fTomo-robot/AK4490DAC/.codex-work/power-layout/after.png

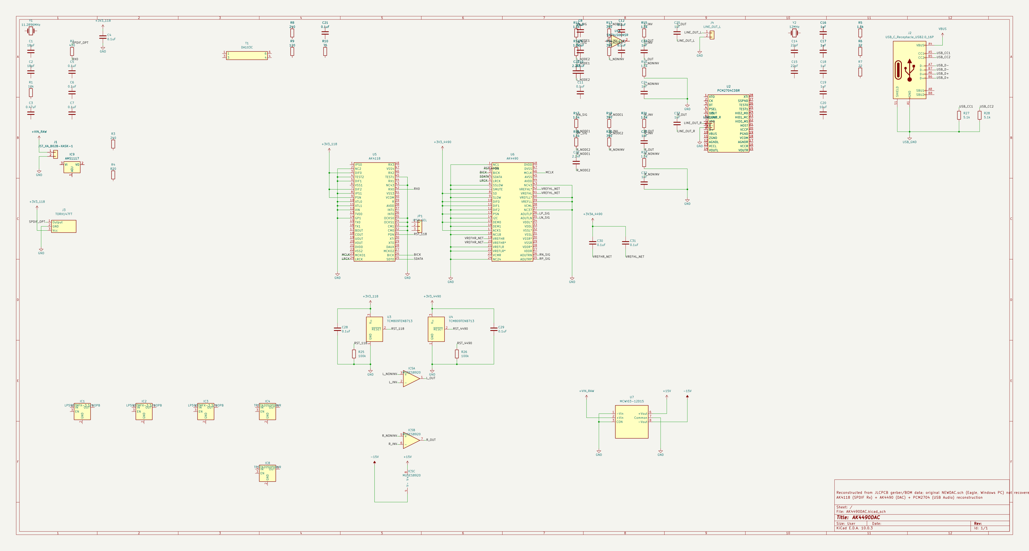
.codex-work/power-layout/after.png
