fTomo-robot/AK4490DAC/.codex-work/power-layout/before.png

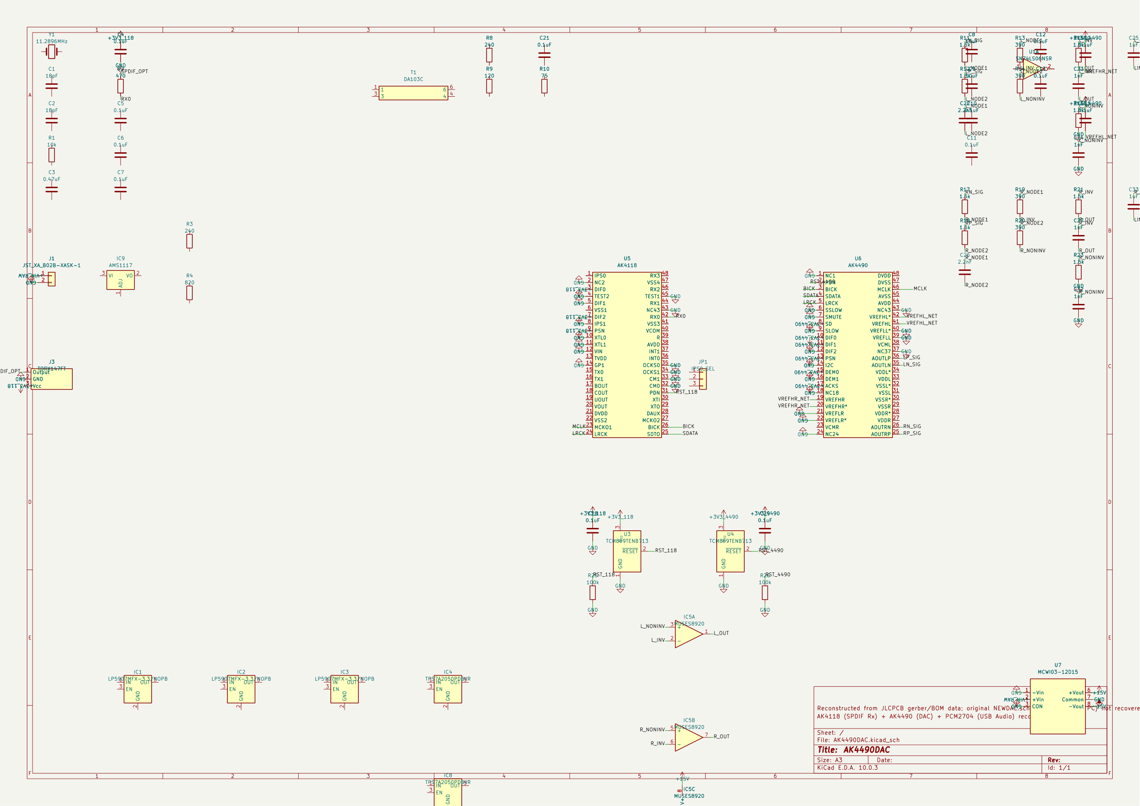
.codex-work/power-layout/before.png
