fTomo-robot/AK4490DAC/.codex-work/power-layout/digital.png

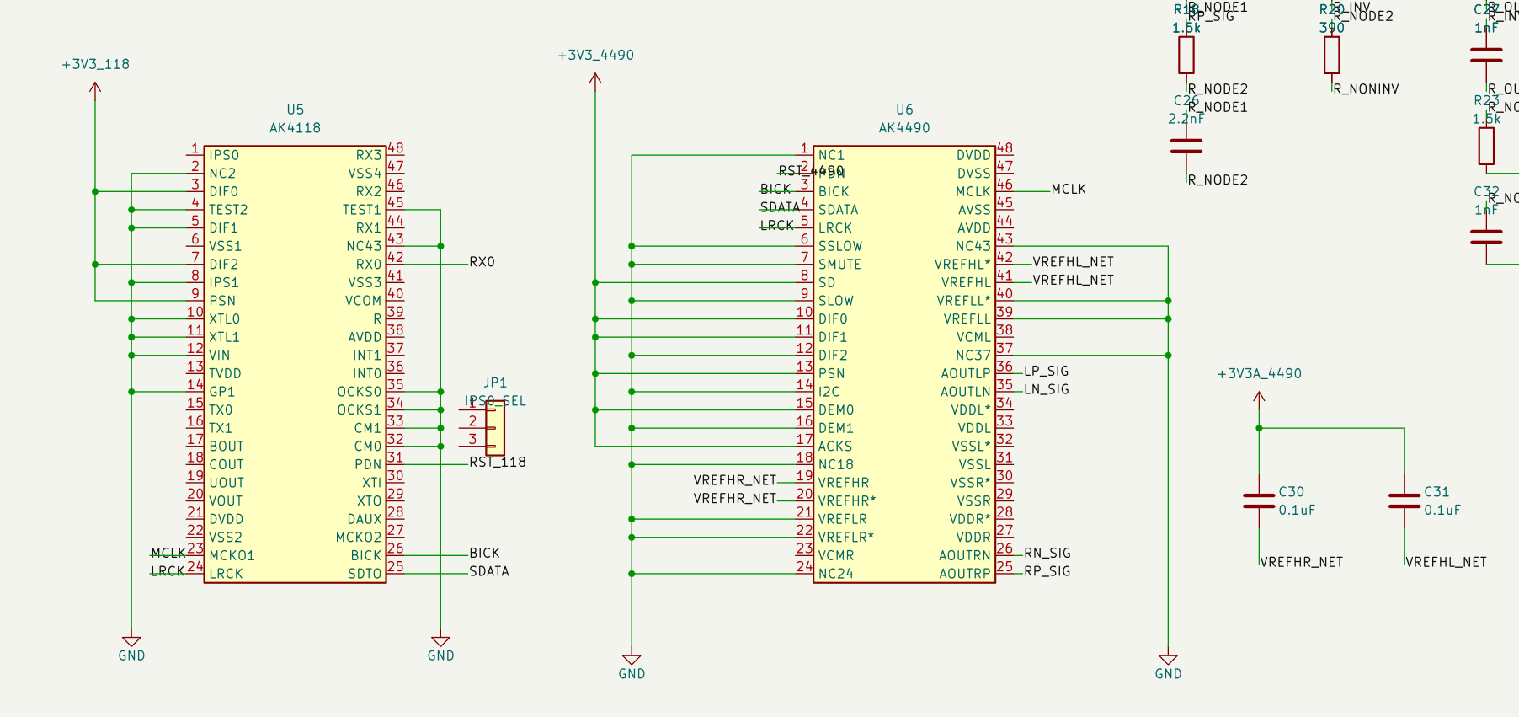
.codex-work/power-layout/digital.png
