fTomo-robot/AK4490DAC/.codex-work/power-layout/input.png

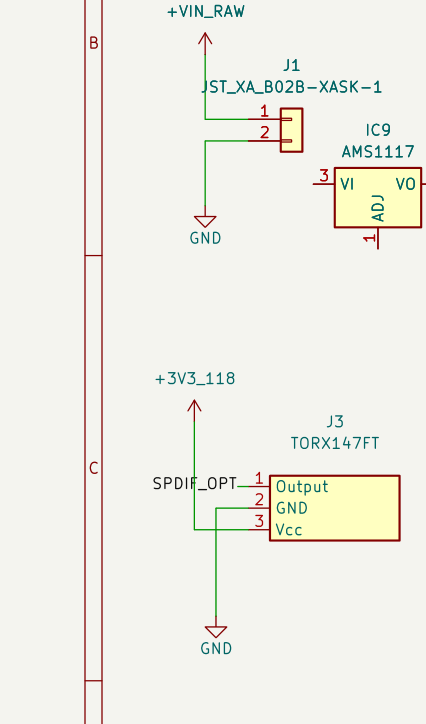
.codex-work/power-layout/input.png
