fTomo-robot/AK4490DAC/.codex-work/power-layout/supply.png

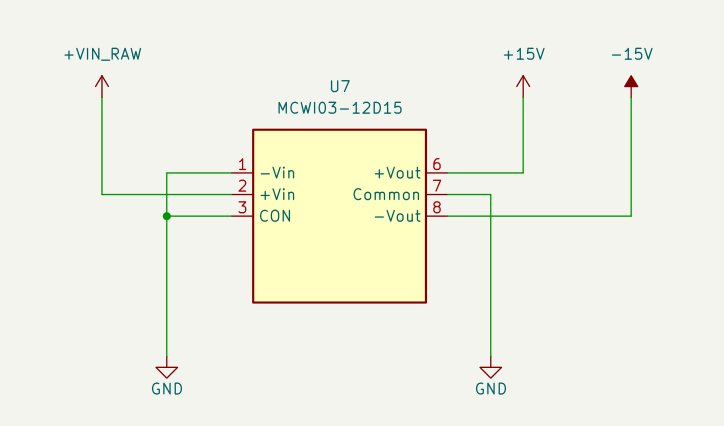
.codex-work/power-layout/supply.png
