fTomo-robot/AK4490DAC/.codex-work/power-layout/usb.png

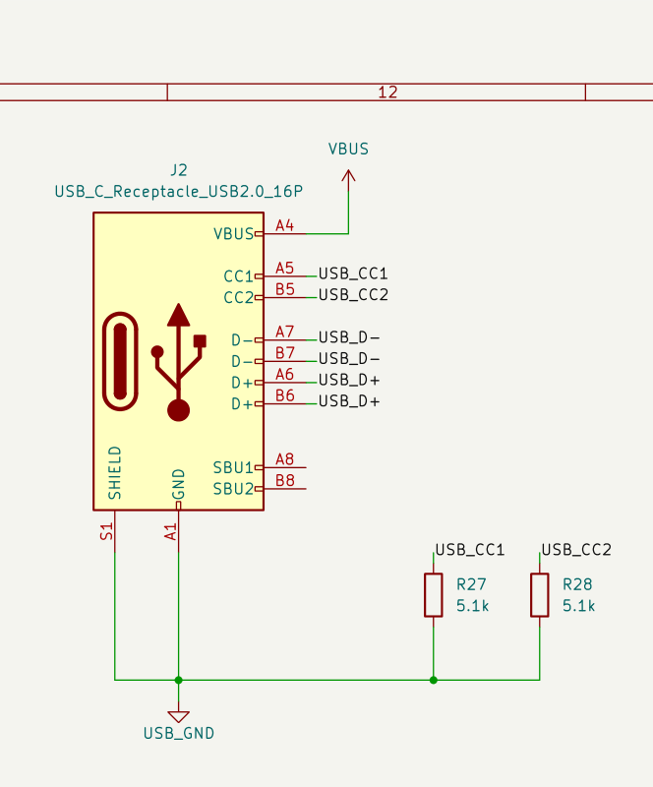
.codex-work/power-layout/usb.png
