fTomo-robot/AK4490DAC/.codex-work/xu316/sources/ak-lpf.png

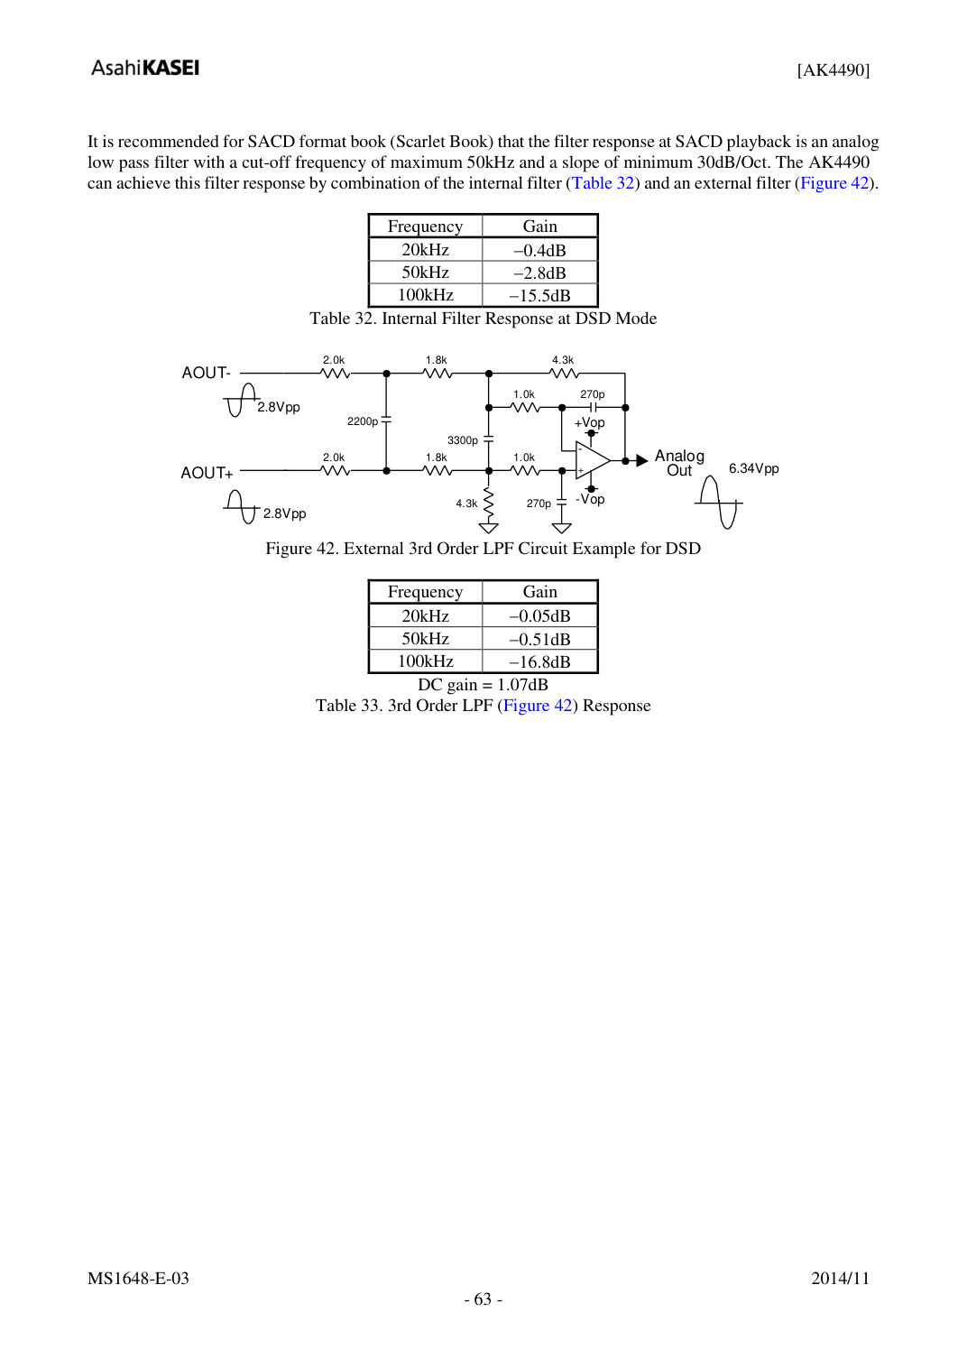
.codex-work/xu316/sources/ak-lpf.png
