fTomo-robot/AK4490DAC/.codex-work/xu316/sources/ak-page60.png

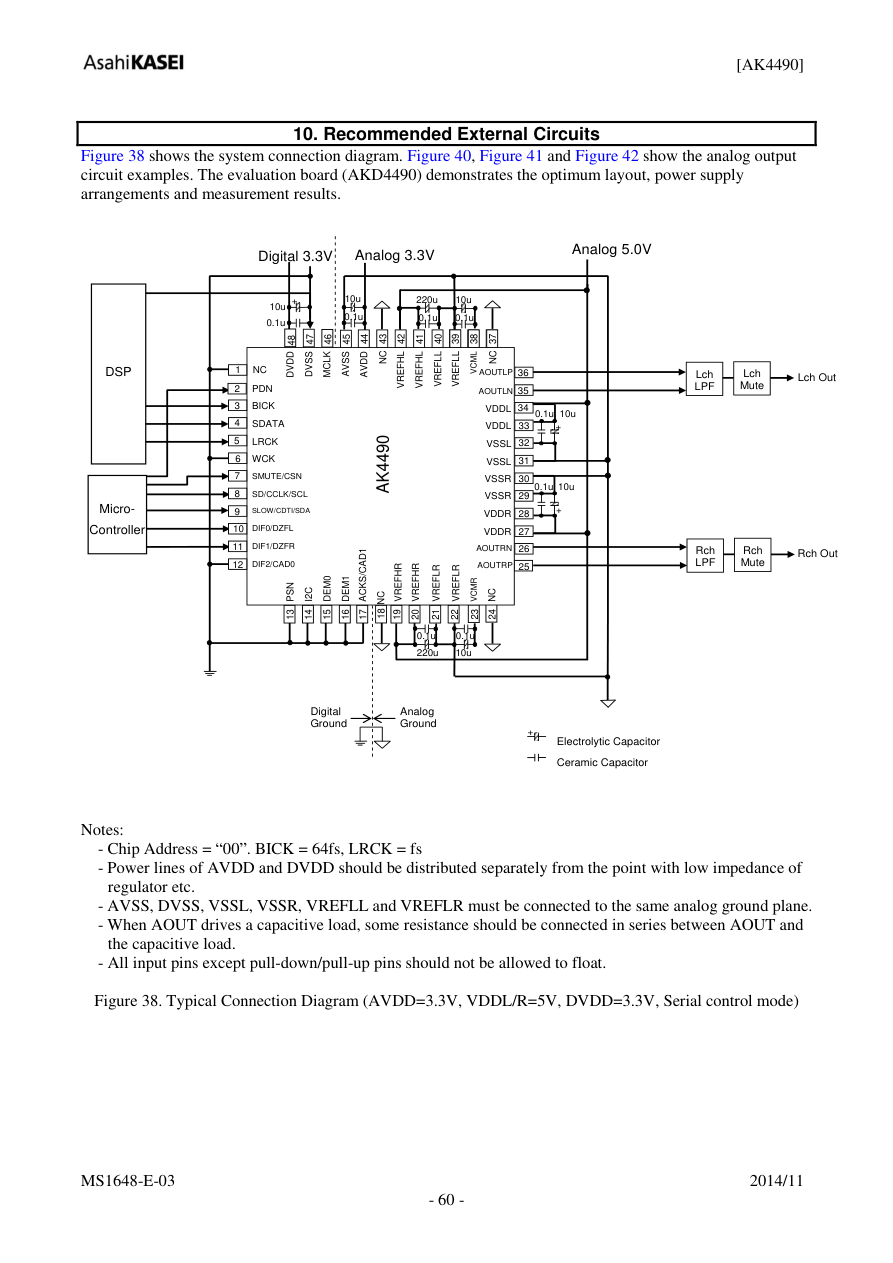
.codex-work/xu316/sources/ak-page60.png
