fTomo-robot/AK4490DAC/.codex-work/xu316/sources/xmos-page49.png

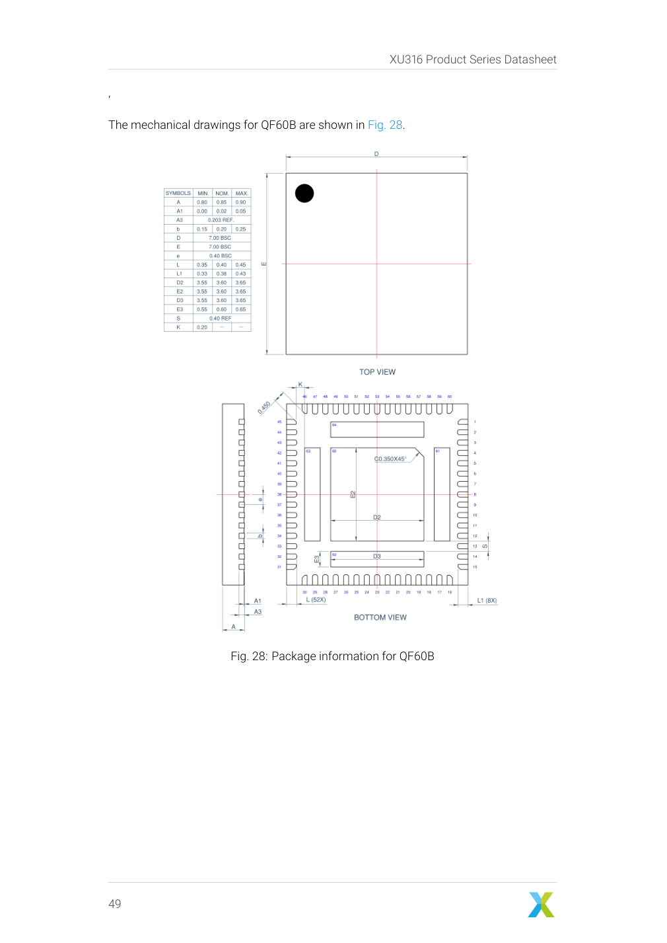
.codex-work/xu316/sources/xmos-page49.png
