fTomo-robot/AK4490DAC/.codex-work/xu316/sources/xmos-page51.png

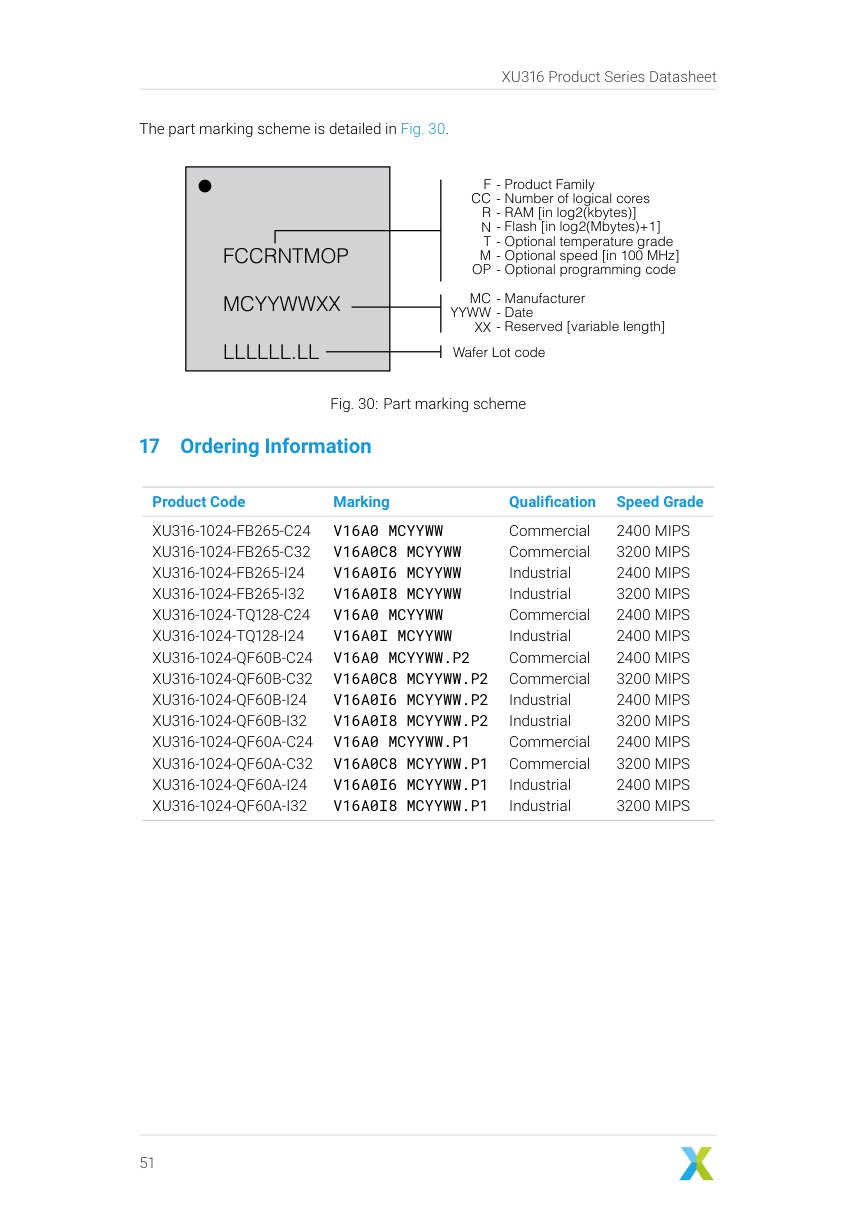
.codex-work/xu316/sources/xmos-page51.png
