fTomo-robot/AK4490DAC/.codex-work/xu316/sources/xmos-page111.png

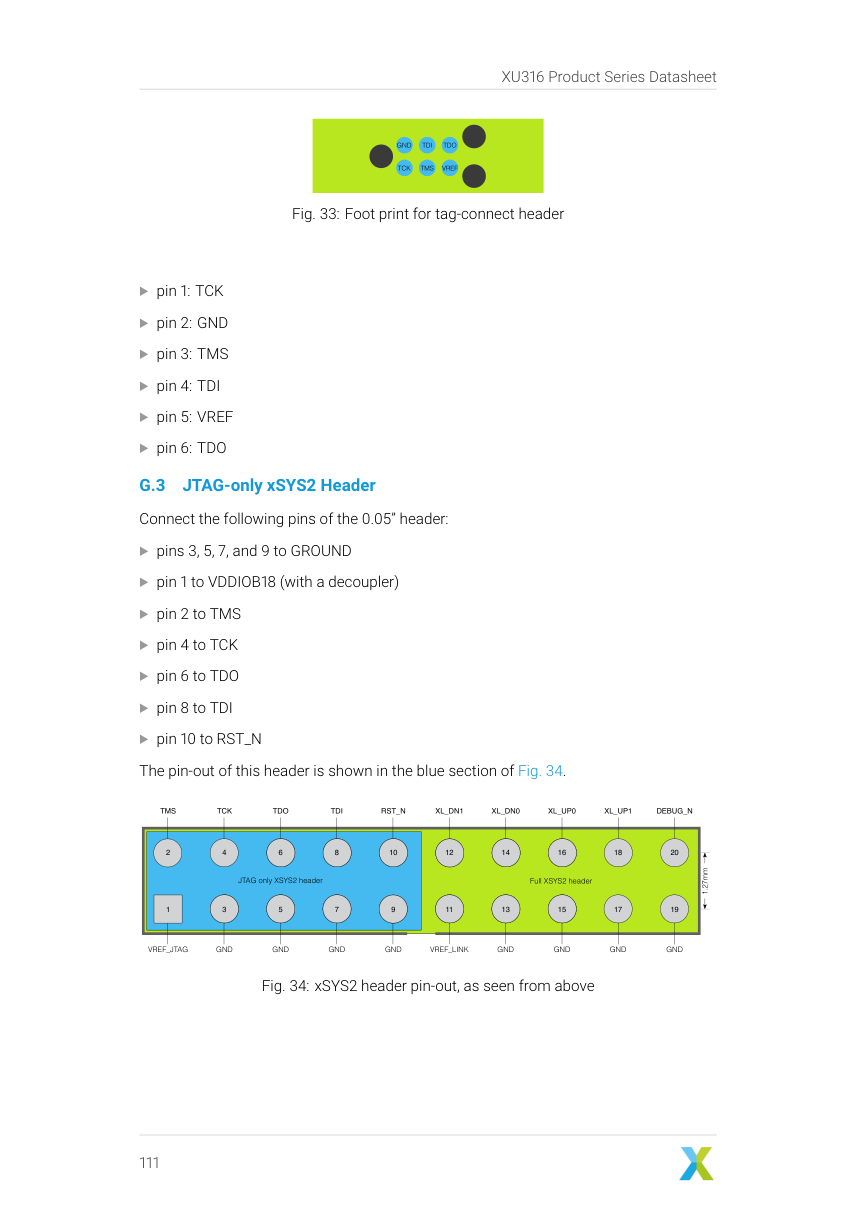
.codex-work/xu316/sources/xmos-page111.png
