fTomo-robot/AK4490DAC/.wiring-cleanup/after.png

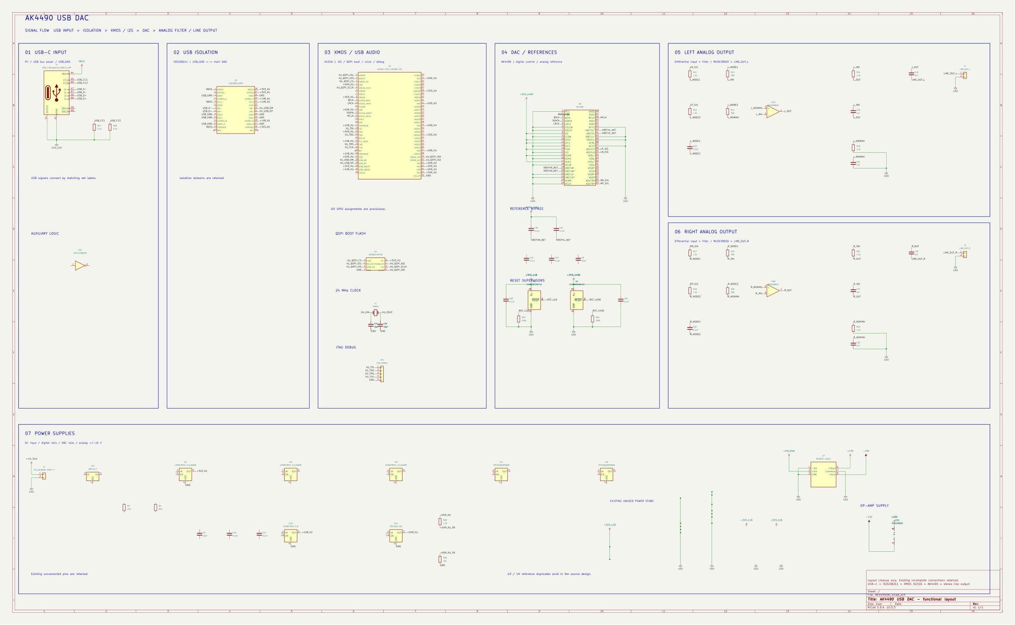
.wiring-cleanup/after.png
