fTomo-robot/AK4490DAC/.wiring-cleanup/before.png

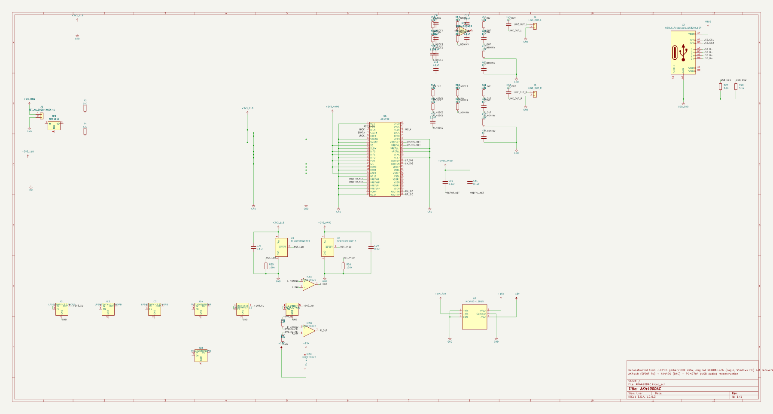
.wiring-cleanup/before.png
