fTomo-robot/AK4490DAC/.wiring-cleanup/final.png

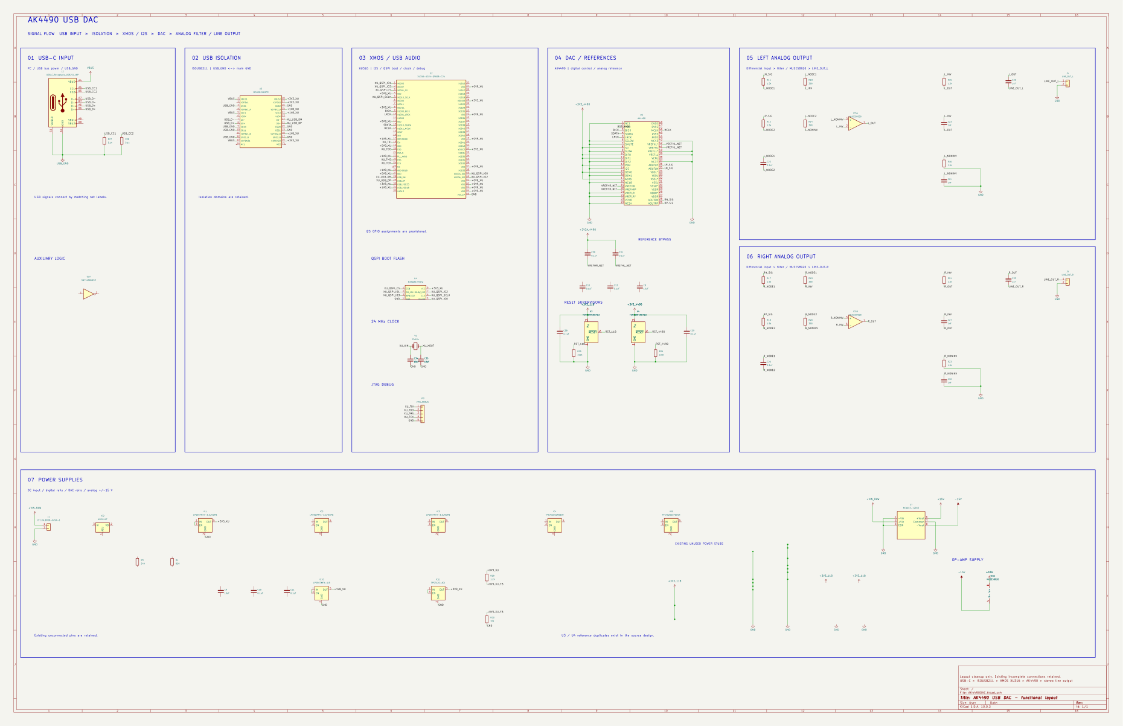
.wiring-cleanup/final.png
