fTomo-robot/AK4490DAC/AK4490DAC.kicad_sch

## KiCad design AK4490DAC.kicad_sch (2026-09-14, an earlier design)

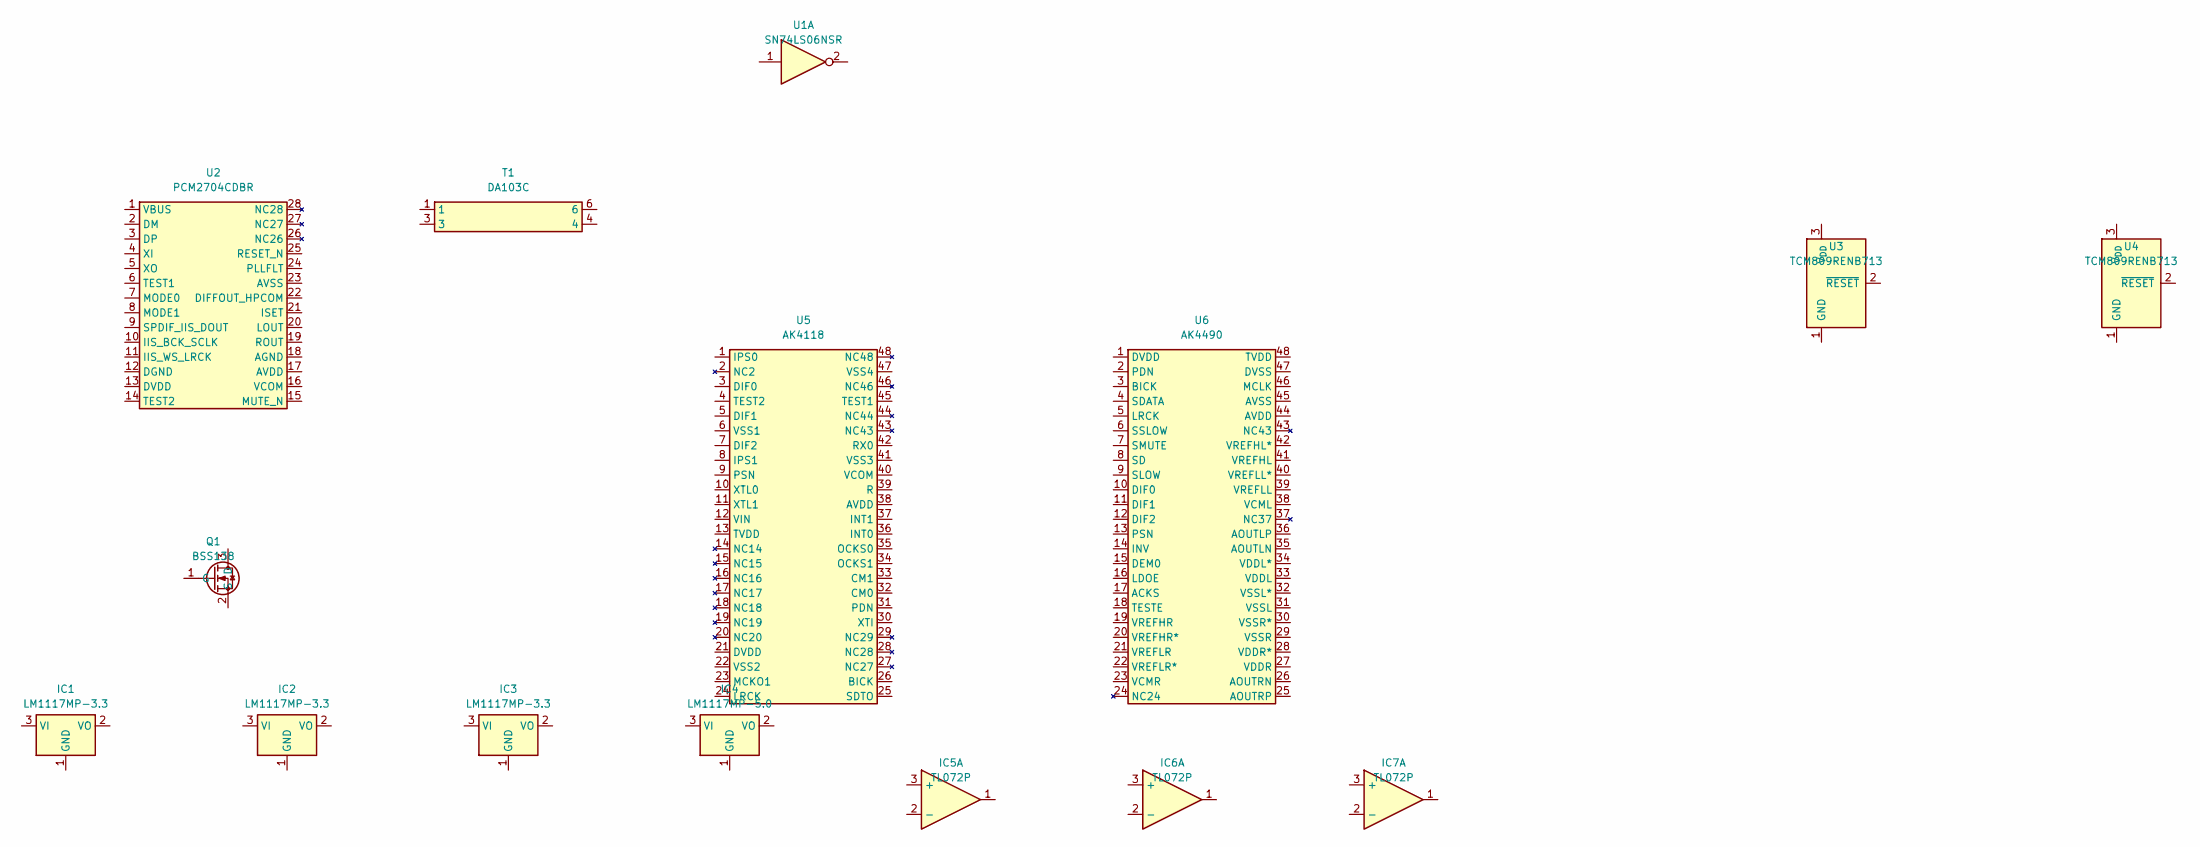
[picture p27: schematic AK4490DAC.kicad_sch]

Parts:
IC1, IC2, IC3: LM1117MP-3.3; SOT-223-3_TabPin2
IC4: LM1117MP-5.0; SOT-223-3_TabPin2
IC5, IC6, IC7: TL072P; DIP-8_W7.62mm
Q1: BSS138; SOT-23
T1: DA103C; DA103C_MUR
U1: SN74LS06NSR; SOIC-14_3.9x8.7mm_P1.27mm
U2: PCM2704CDBR; SSOP-28_5.3x10.2mm_P0.65mm
U3, U4: TCM809RENB713; SOT-23
U5: AK4118; LQFP-48_7x7mm_P0.5mm
U6: AK4490; LQFP-48_7x7mm_P0.5mm
