fTomo-robot/AK4490DAC/.wiring-cleanup/before.kicad_sch

## KiCad design .wiring-cleanup/before.kicad_sch (2026-09-13)

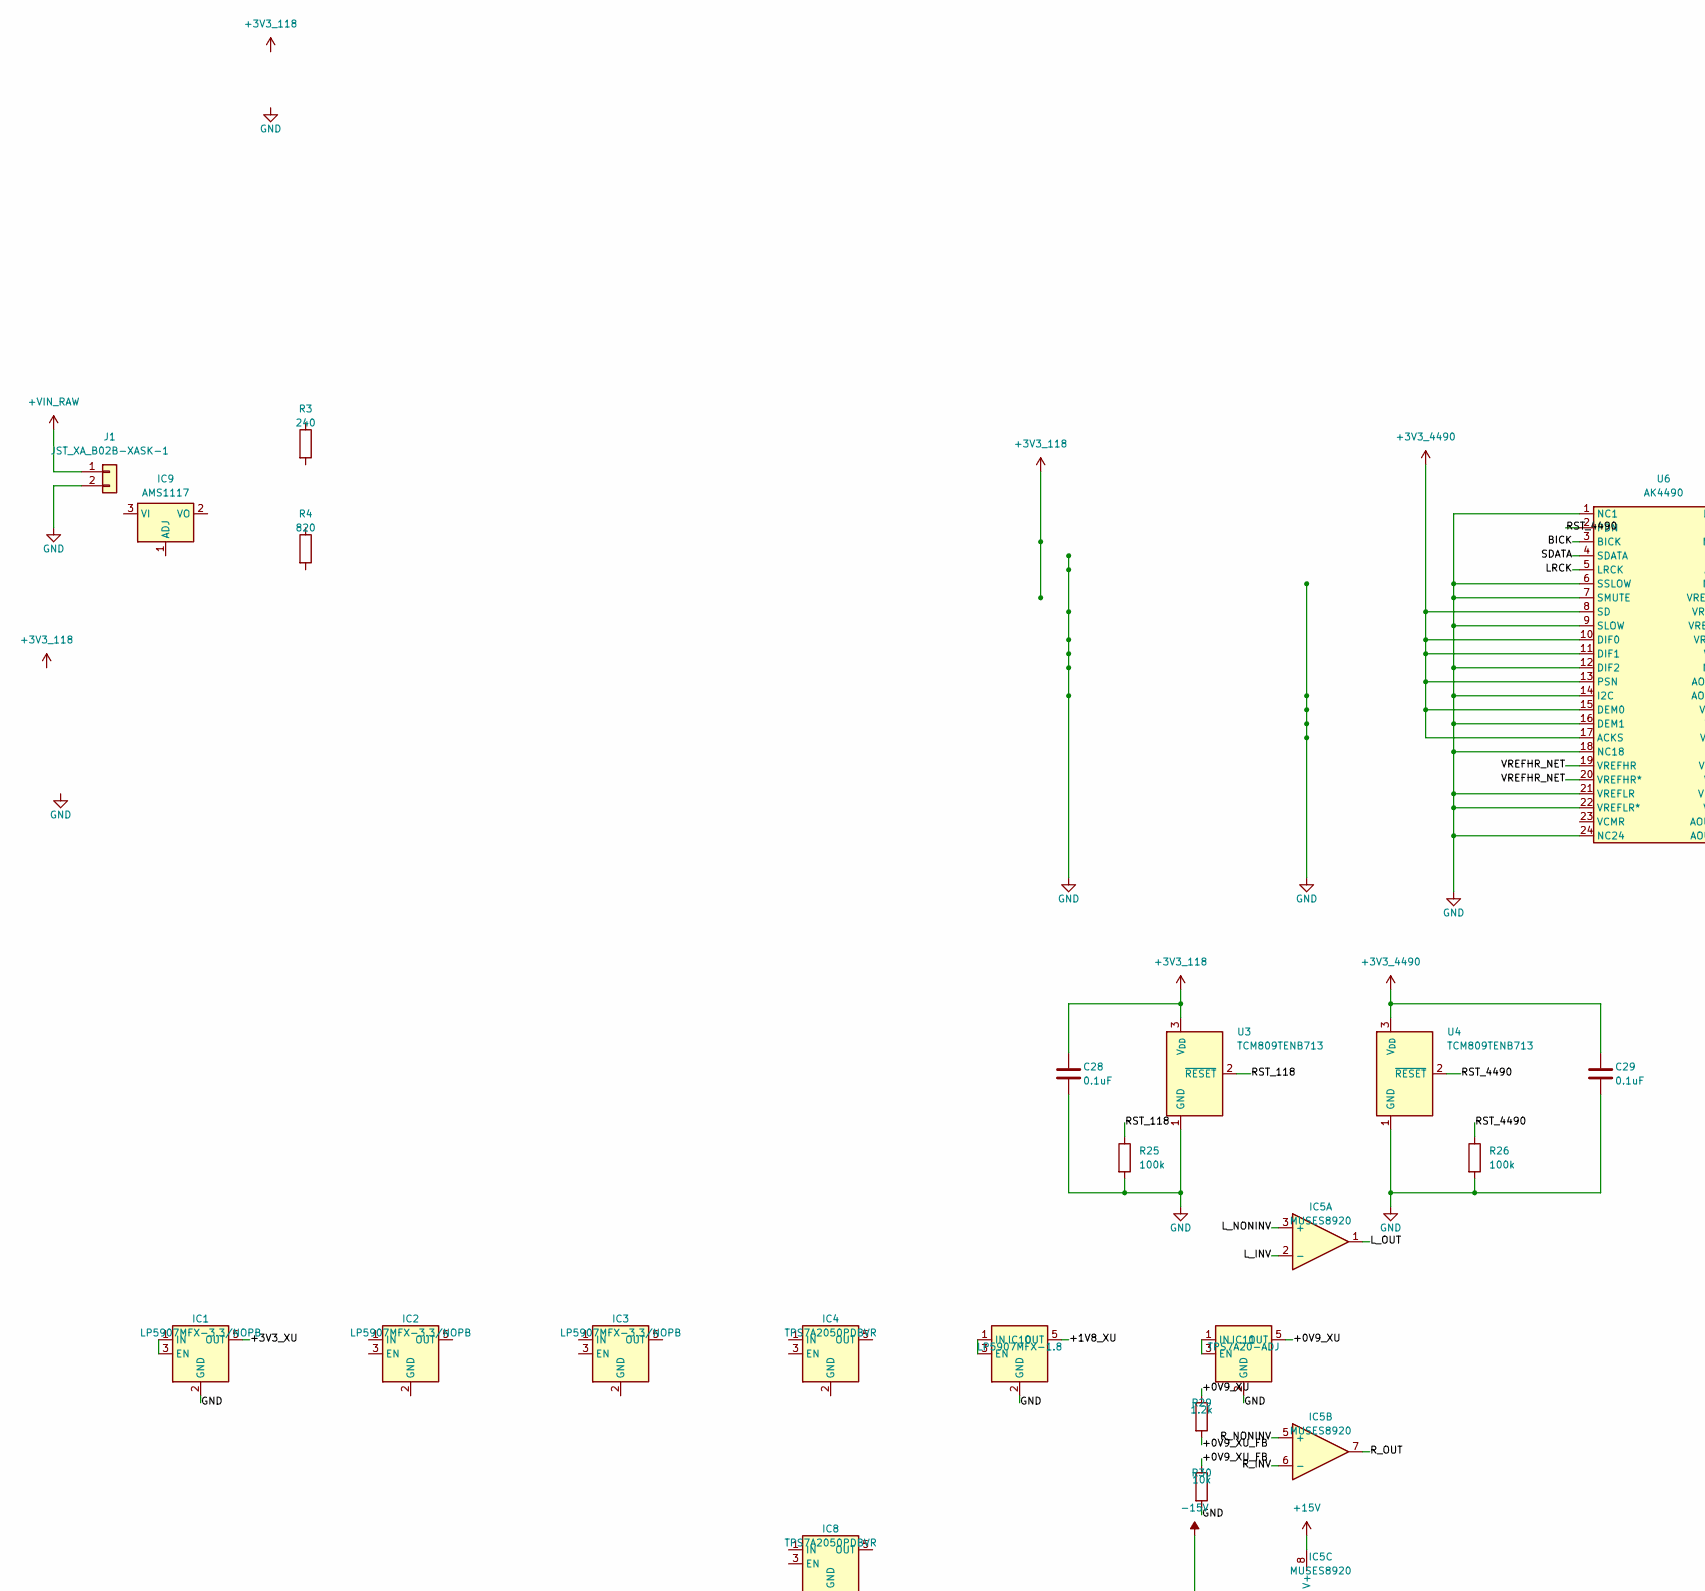
[picture p28: schematic before.kicad_sch, part in row 1, column 1]

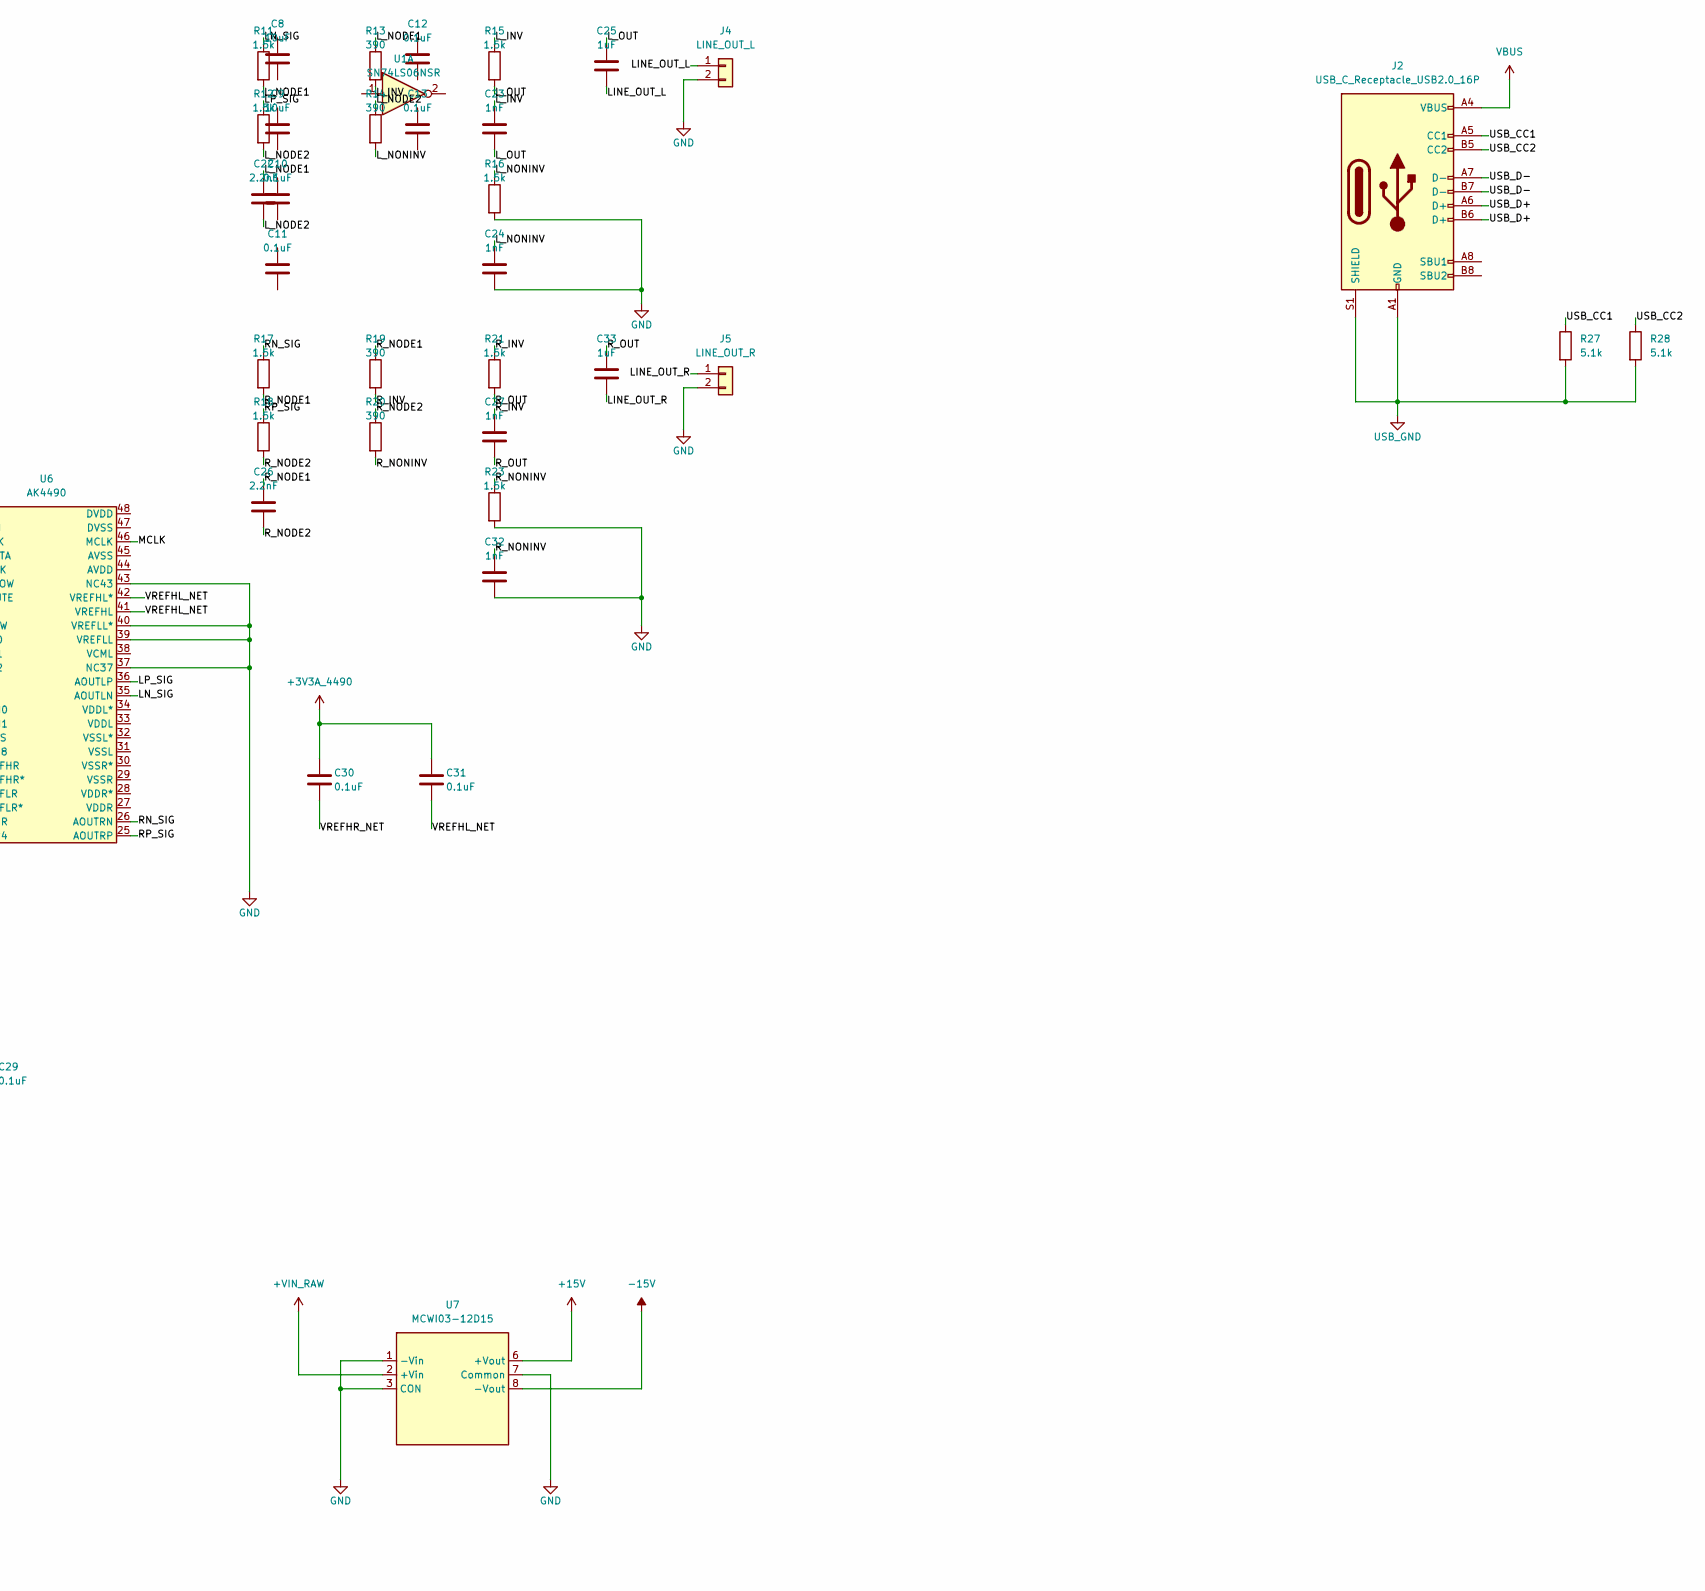
[picture p29: schematic before.kicad_sch, part in row 1, column 2]

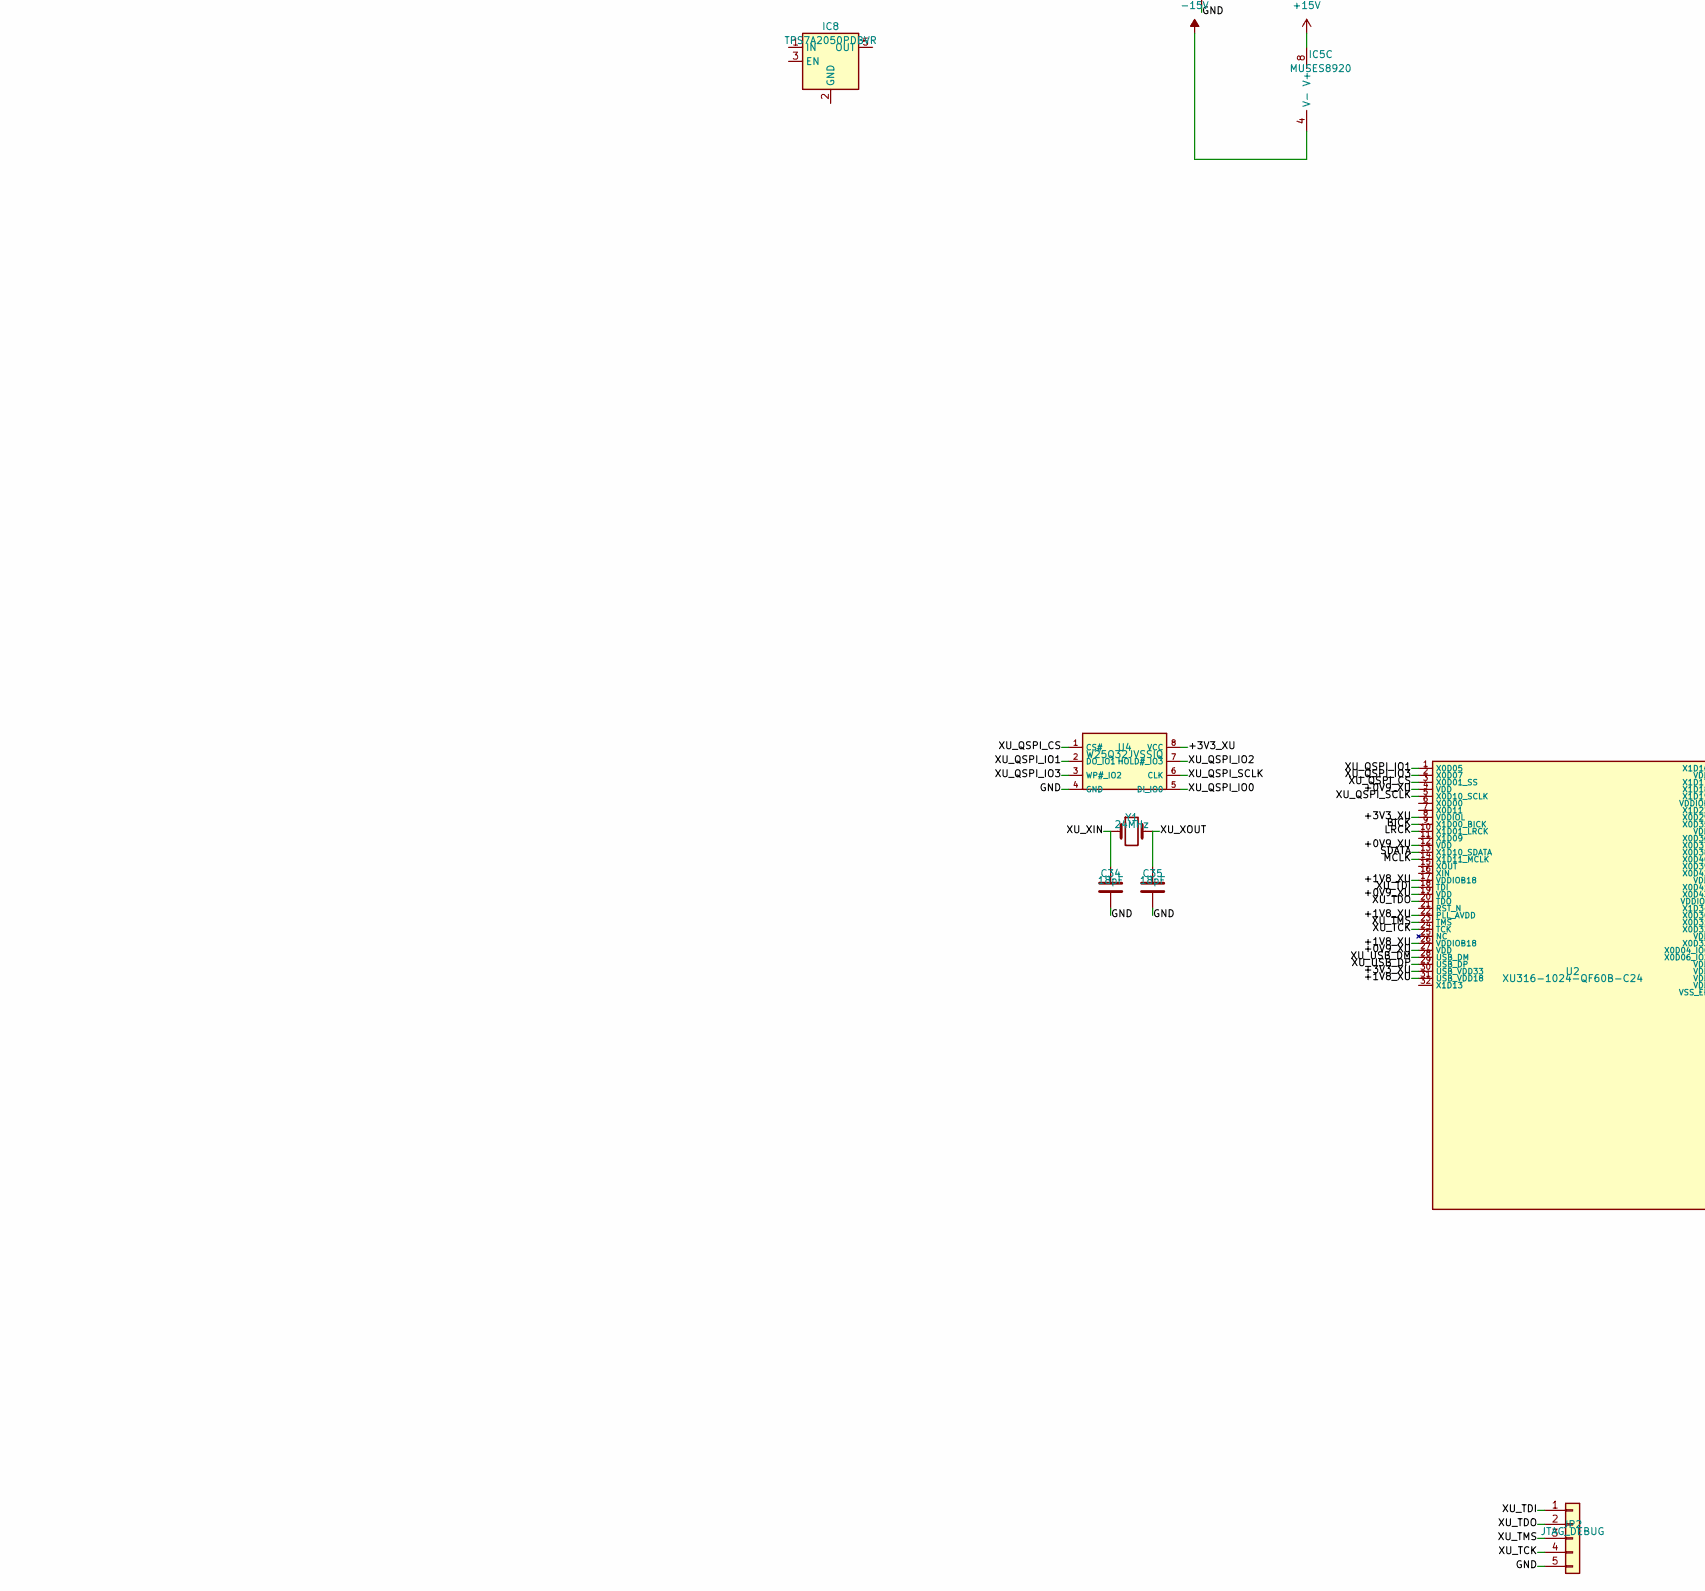
[picture p30: schematic before.kicad_sch, part in row 2, column 1]

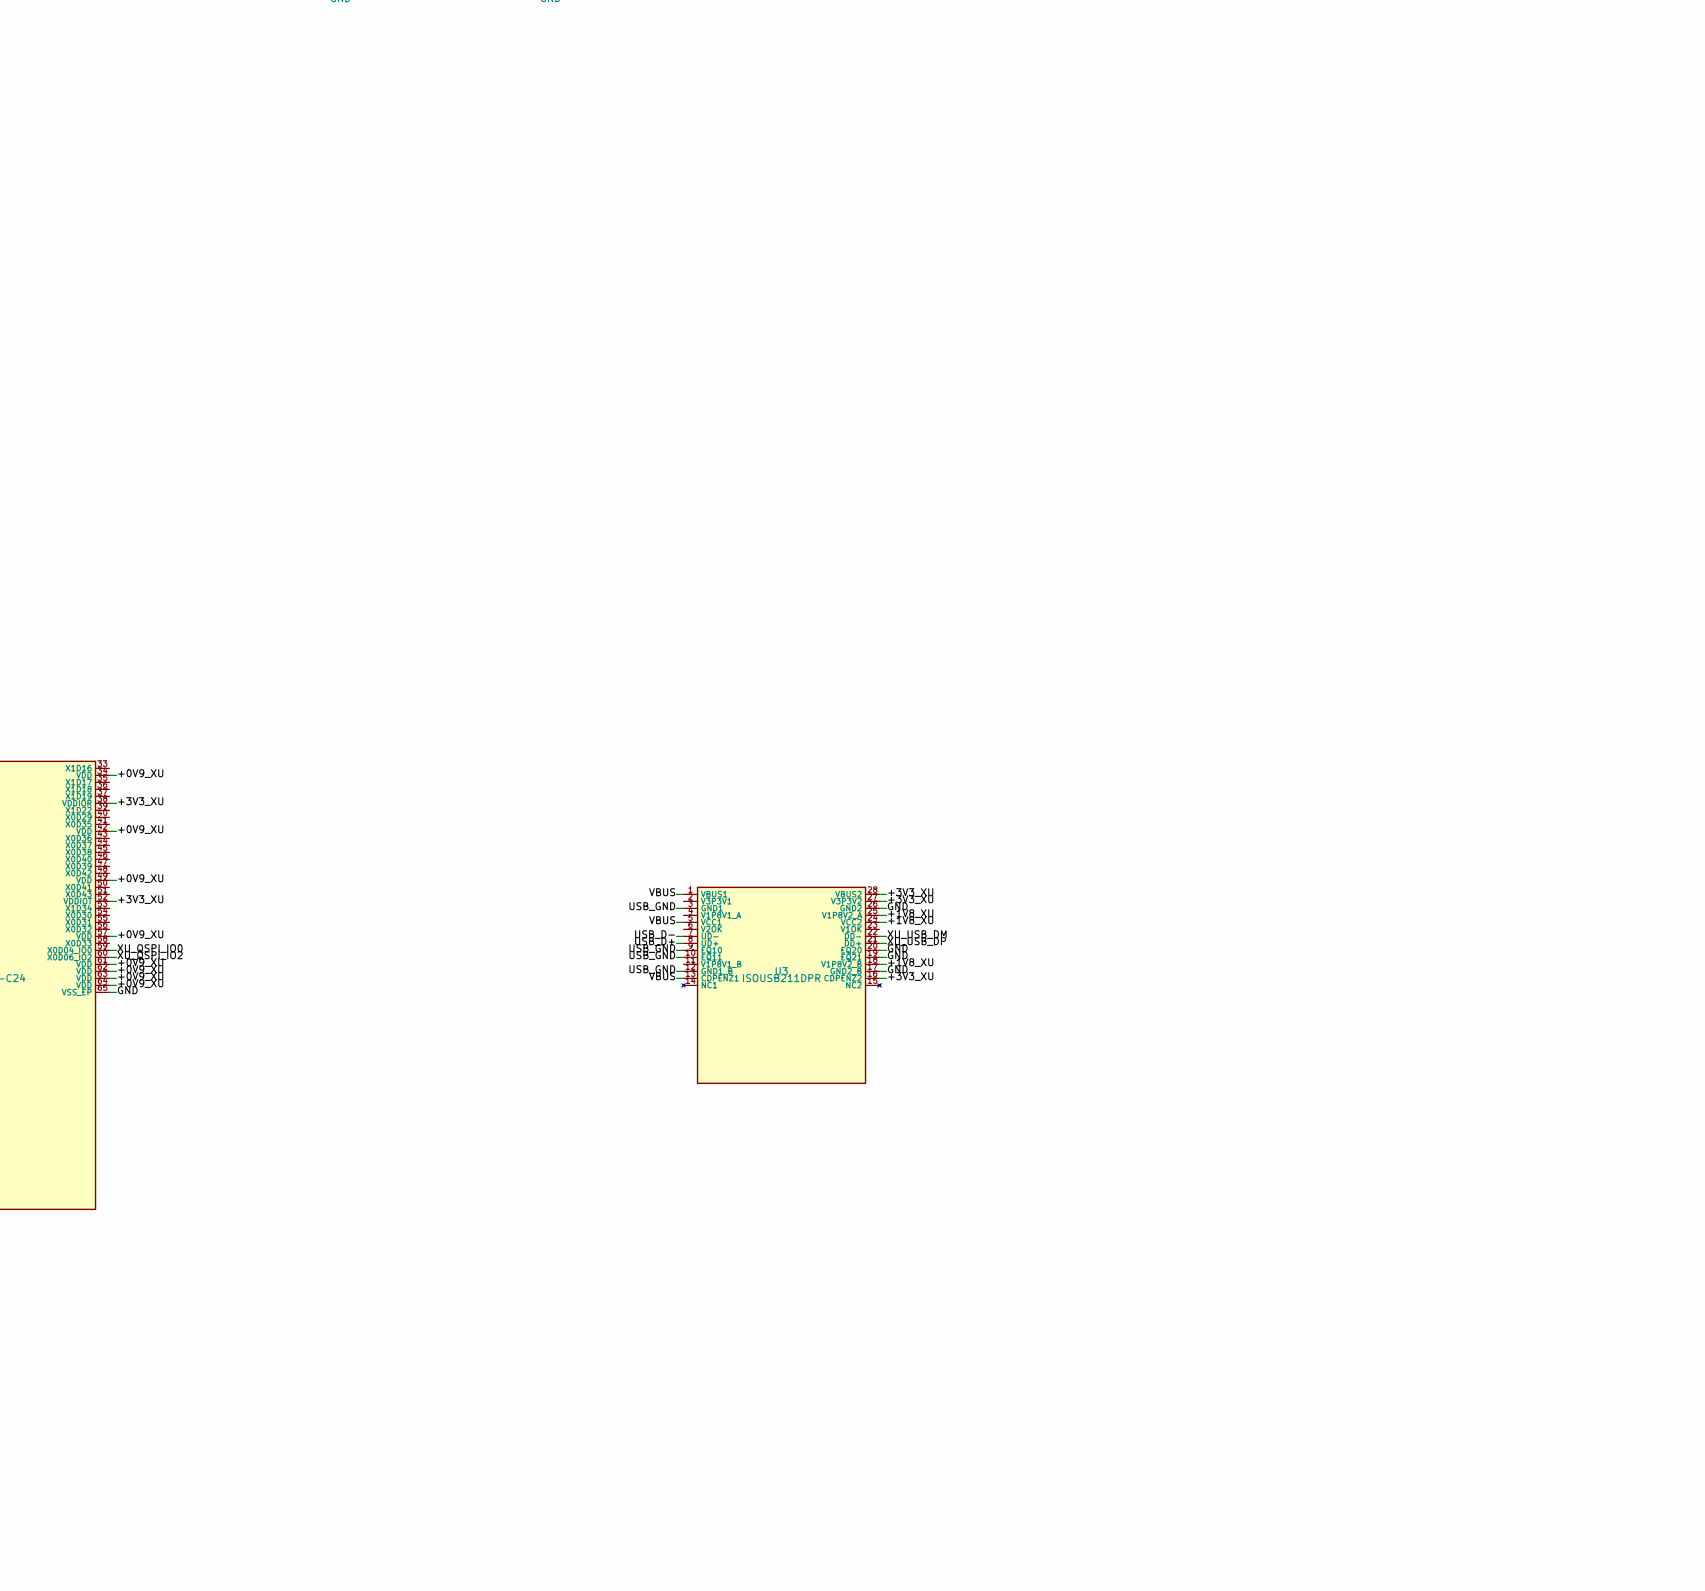
[picture p31: schematic before.kicad_sch, part in row 2, column 2]

Parts:
C8, C9: 10uF; C_0805_2012Metric
C10, C11, C12, C13, C28, C29, C30, C31: 0.1uF; C_0603_1608Metric
C22, C26: 2.2nF; C_0603_1608Metric
C23, C24, C27, C32: 1nF; C_0603_1608Metric
C25, C33: 1uF; C_0603_1608Metric
C34, C35: 18pF; C_0603_1608Metric
IC1, IC2, IC3: LP5907MFX-3.3/NOPB; SOT-23-5
IC4, IC8: TPS7A2050PDBVR; SOT-23-5
IC5: MUSES8920; DIP-8_W7.62mm
IC9: AMS1117; SOT-223-3_TabPin2
IC10: LP5907MFX-1.8; SOT-23-5
IC11: TPS7A20-ADJ; SOT-23-5
J1: JST_XA_B02B-XASK-1; JST_XA_B02B-XASK-1_1x02_P2.50mm_Vertical
J2: USB_C_Receptacle_USB2.0_16P; USB_C_Receptacle_GCT_USB4085
J4: LINE_OUT_L
J5: LINE_OUT_R
JP2: JTAG_DEBUG; PinHeader_1x05_P2.54mm_Vertical
R3: 240; R_0603_1608Metric
R4: 820; R_0603_1608Metric
R11, R12, R15, R16, R17, R18, R21, R23: 1.5k; R_0603_1608Metric
R13, R14, R19, R20: 390; R_0603_1608Metric
R25, R26: 100k; R_0603_1608Metric
R27, R28: 5.1k; R_0603_1608Metric
R29: 1.2k; R_0603_1608Metric
R30: 10k; R_0603_1608Metric
U1: SN74LS06NSR; SOIC-14_3.9x8.7mm_P1.27mm
U2: XU316-1024-QF60B-C24; XU316_QF60B_7x7
U3, U4: TCM809TENB713; SOT-23
U6: AK4490; LQFP-48_7x7mm_P0.5mm
U7: MCWI03-12D15
Y1: 24MHz; Crystal_SMD_3225-4Pin_3.2x2.5mm

Connections:
+0V9_XU: IC11.5 (OUT), R29.1, U2.4 (VDD), U2.12 (VDD), U2.19 (VDD), U2.27 (VDD), U2.34 (VDD), U2.42 (VDD), U2.49 (VDD), U2.57 (VDD), U2.61 (VDD), U2.62 (VDD), U2.63 (VDD), U2.64 (VDD)
+0V9_XU_FB: R29.2, R30.1
+1V8_XU: IC10.5 (OUT), U2.17 (VDDIOB18), U2.22 (PLL_AVDD), U2.26 (VDDIOB18), U2.31 (USB_VDD18), U3.18 (V1P8V2_B), U3.24 (VCC2), U3.25 (V1P8V2_A)
+3V3A_4490: C30.1, C31.1
+3V3_118: C28.1, U3.3 (GND1)
+3V3_4490: C29.1, U4.3 (WP#_IO2), U6.8 (SD), U6.10 (DIF0), U6.11 (DIF1), U6.13 (PSN), U6.15 (DEM0), U6.17 (ACKS)
+3V3_XU: IC1.5 (OUT), U2.8 (VDDIOL), U2.30 (USB_VDD33), U2.38 (VDDIOR), U2.52 (VDDIOT), U3.16 (CDPENZ2), U3.27 (V3P3V2), U3.28 (VBUS2), U4.8 (VCC)
+15V: IC5.8 (V+), U7.6 (+Vout)
+VIN_RAW: J1.1, U7.2 (+Vin)
-15V: IC5.4 (V-), U7.8 (-Vout)
BICK: U2.9 (X1D00_BICK), U6.3 (BICK)
GND: C24.2, C28.2, C29.2, C32.2, C34.2, C35.2, IC1.2 (GND), IC10.2 (GND), IC11.2 (GND), J1.2, J4.2, J5.2, JP2.5, R16.2, R23.2, R25.2, R26.2, R30.2, U2.65 (VSS_EP), U3.1 (VBUS1), U3.17 (GND2_B), U3.19 (EQ21), U3.20 (EQ20), U3.26 (GND2), U4.1 (CS#), U4.4 (GND), U6.1 (NC1), U6.6 (SSLOW), U6.7 (SMUTE), U6.9 (SLOW), U6.12 (DIF2), U6.14 (I2C), U6.16 (DEM1), U6.18 (NC18), U6.21 (VREFLR), U6.22 (VREFLR*), U6.24 (NC24), U6.37 (NC37), U6.39 (VREFLL), U6.40 (VREFLL*), U6.43 (NC43), U7.1 (-Vin), U7.3 (CON), U7.7 (Common)
LINE_OUT_L: C25.2, J4.1
LINE_OUT_R: C33.2, J5.1
LN_SIG: R11.1, U6.35 (AOUTLN)
LP_SIG: R12.1, U6.36 (AOUTLP)
LRCK: U2.10 (X1D01_LRCK), U6.5 (LRCK)
L_INV: C23.1, IC5.2 (-), R13.2, R15.1
L_NODE1: C22.1, R11.2, R13.1
L_NODE2: C22.2, R12.2, R14.1
L_NONINV: C24.1, IC5.3 (+), R14.2, R16.1
L_OUT: C23.2, C25.1, IC5.1, R15.2
MCLK: U2.14 (X1D11_MCLK), U6.46 (MCLK)
unnamed: IC1.1 (IN), IC1.3 (EN)
unnamed: IC10.1 (IN), IC10.3 (EN)
unnamed: IC11.1 (IN), IC11.3 (EN)
RN_SIG: R17.1, U6.26 (AOUTRN)
RP_SIG: R18.1, U6.25 (AOUTRP)
RST_118: R25.1, U3.2 (V3P3V1)
RST_4490: R26.1, U4.2 (DO_IO1), U6.2 (PDN)
R_INV: C27.1, IC5.6 (-), R19.2, R21.1
R_NODE1: C26.1, R17.2, R19.1
R_NODE2: C26.2, R18.2, R20.1
R_NONINV: C32.1, IC5.5 (+), R20.2, R23.1
R_OUT: C27.2, C33.1, IC5.7, R21.2
SDATA: U2.13 (X1D10_SDATA), U6.4 (SDATA)
USB_CC1: J2.A5 (CC1), R27.1
USB_CC2: J2.B5 (CC2), R28.1
USB_D+: J2.A6 (D+), J2.B6 (D+), U3.8 (UD+)
USB_D-: J2.A7 (D-), J2.B7 (D-), U3.7 (UD-)
USB_GND: J2.A1 (GND), J2.A12 (GND), J2.B1 (GND), J2.B12 (GND), J2.S1 (SHIELD), R27.2, R28.2, U3.3 (GND1), U3.9 (EQ10), U3.10 (EQ11), U3.12 (GND1_B)
VBUS: J2.A4 (VBUS), J2.A9 (VBUS), J2.B4 (VBUS), J2.B9 (VBUS), U3.1 (VBUS1), U3.5 (VCC1), U3.13 (CDPENZ1)
VREFHL_NET: C31.2, U6.41 (VREFHL), U6.42 (VREFHL*)
VREFHR_NET: C30.2, U6.19 (VREFHR), U6.20 (VREFHR*)
XU_QSPI_CS: U2.3 (X0D01_SS), U4.1 (CS#)
XU_QSPI_IO0: U2.59 (X0D04_IO0), U4.5 (DI_IO0)
XU_QSPI_IO1: U2.1 (X0D05), U4.2 (DO_IO1)
XU_QSPI_IO2: U2.60 (X0D06_IO2), U4.7 (HOLD#_IO3)
XU_QSPI_IO3: U2.2 (X0D07), U4.3 (WP#_IO2)
XU_QSPI_SCLK: U2.5 (X0D10_SCLK), U4.6 (CLK)
XU_TCK: JP2.4, U2.24 (TCK)
XU_TDI: JP2.1, U2.18 (TDI)
XU_TDO: JP2.2, U2.20 (TDO)
XU_TMS: JP2.3, U2.23 (TMS)
XU_USB_DM: U2.28 (USB_DM), U3.22 (DD-)
XU_USB_DP: U2.29 (USB_DP), U3.21 (DD+)
XU_XIN: C34.1, Y1.1
XU_XOUT: C35.1, Y1.2
