fTomo-robot/AK4490DAC/.codex-work/power-cleanup/before.kicad_sch

## KiCad design .codex-work/power-cleanup/before.kicad_sch (2026-09-14)

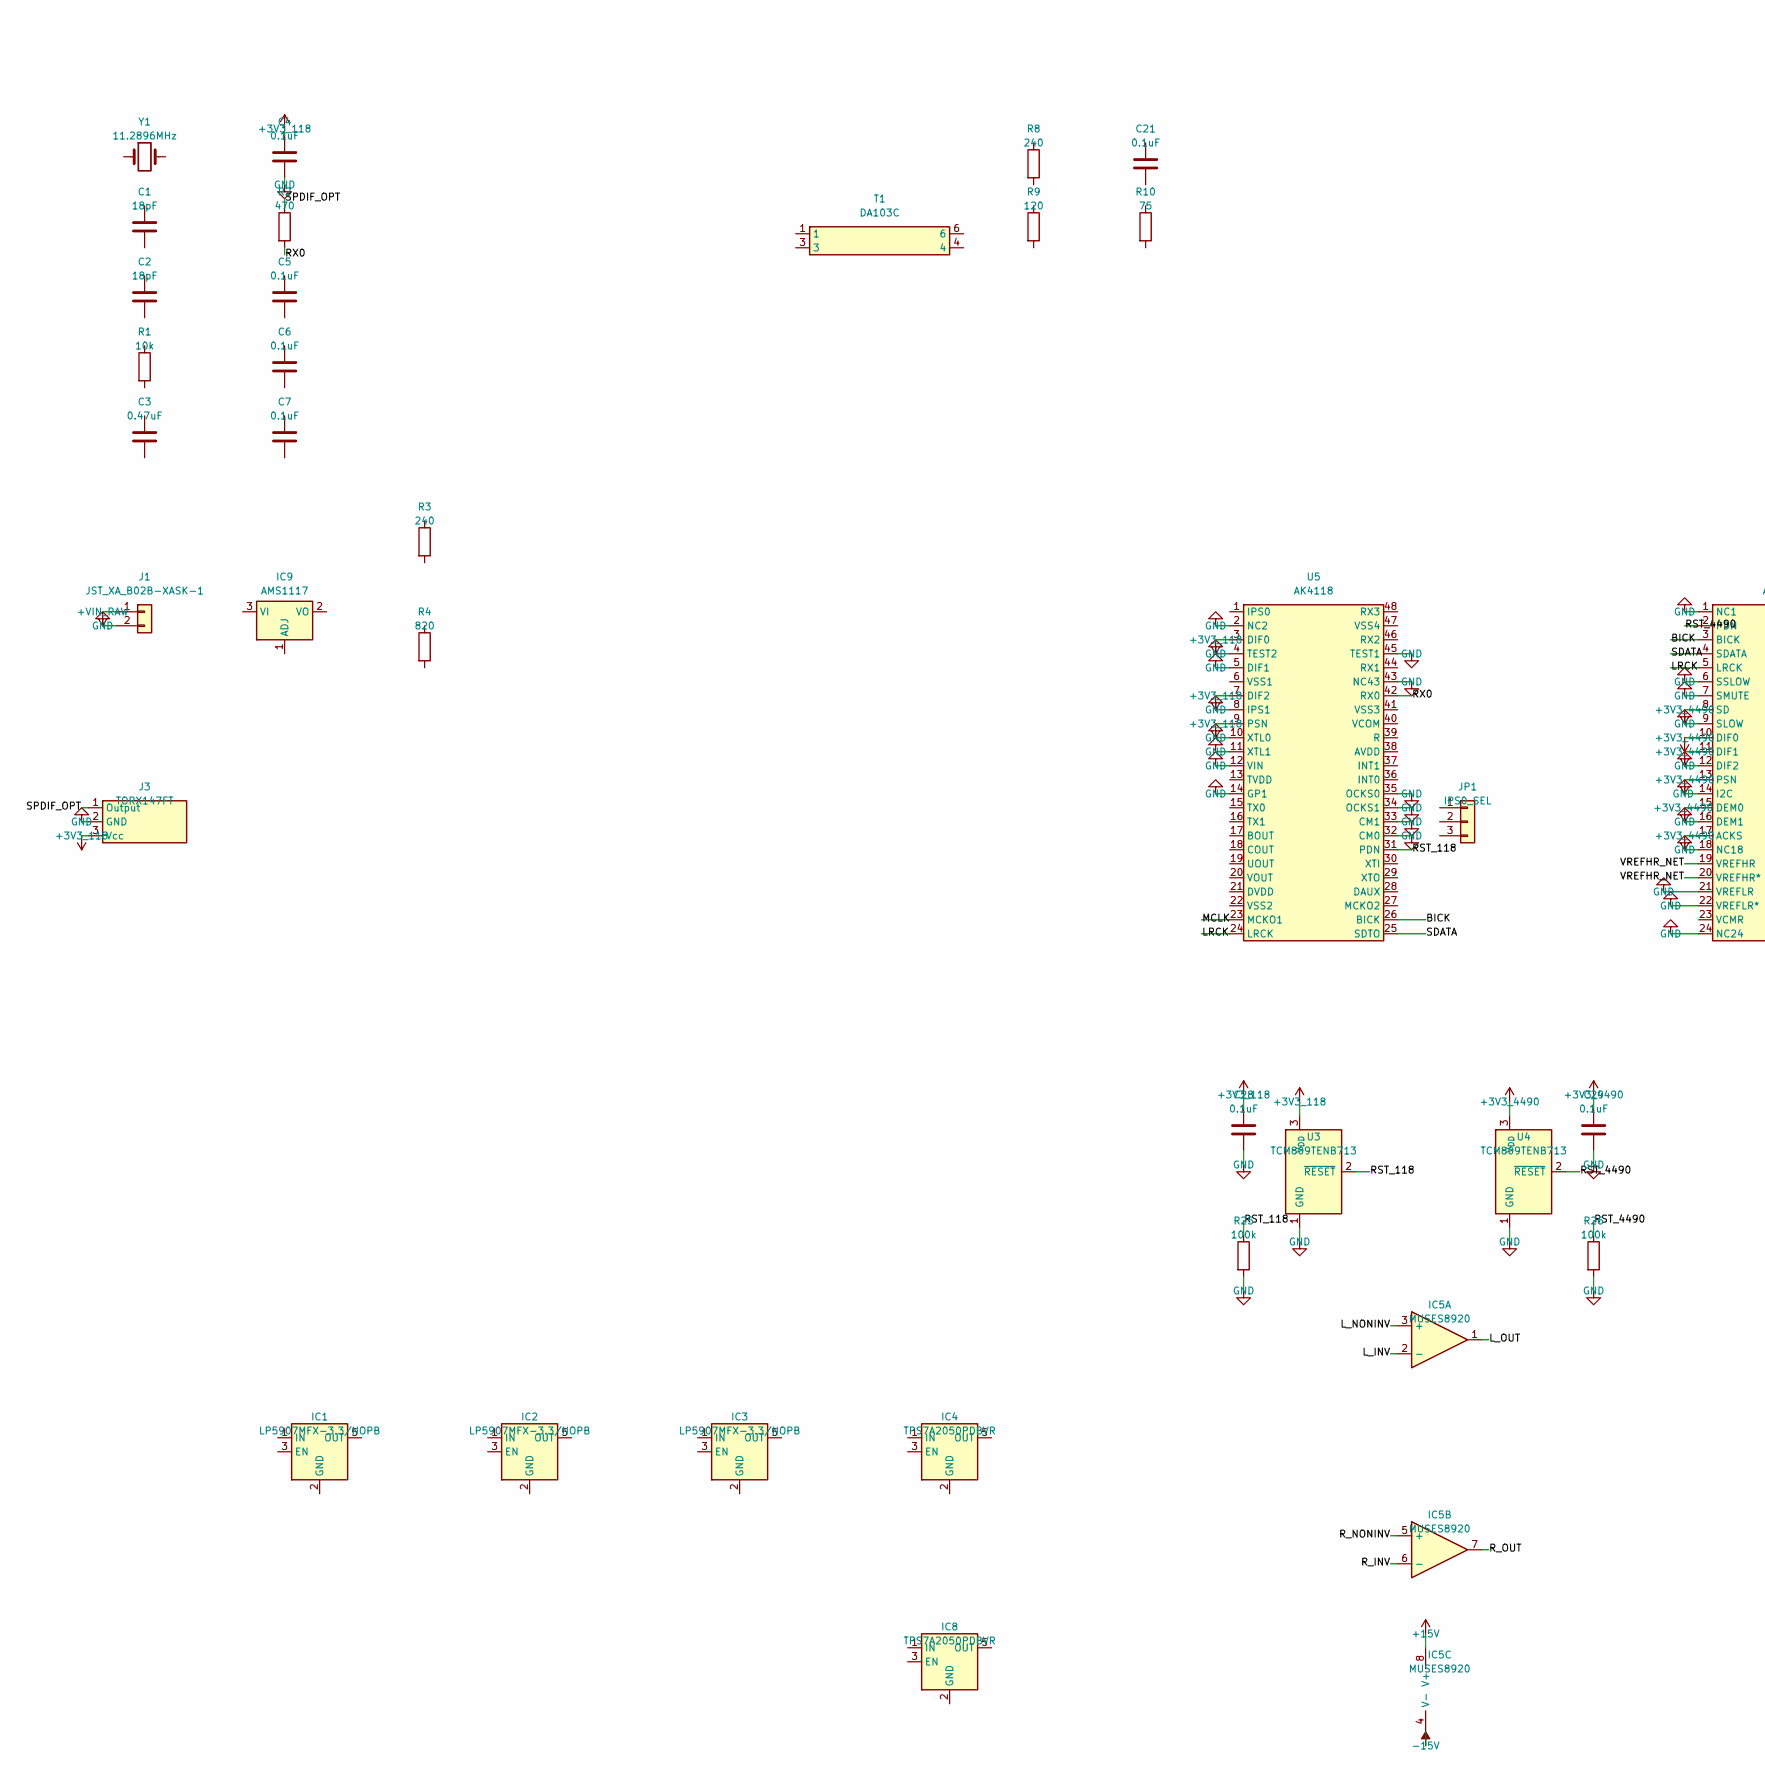
[picture p32: schematic before.kicad_sch, part in row 1, column 1]

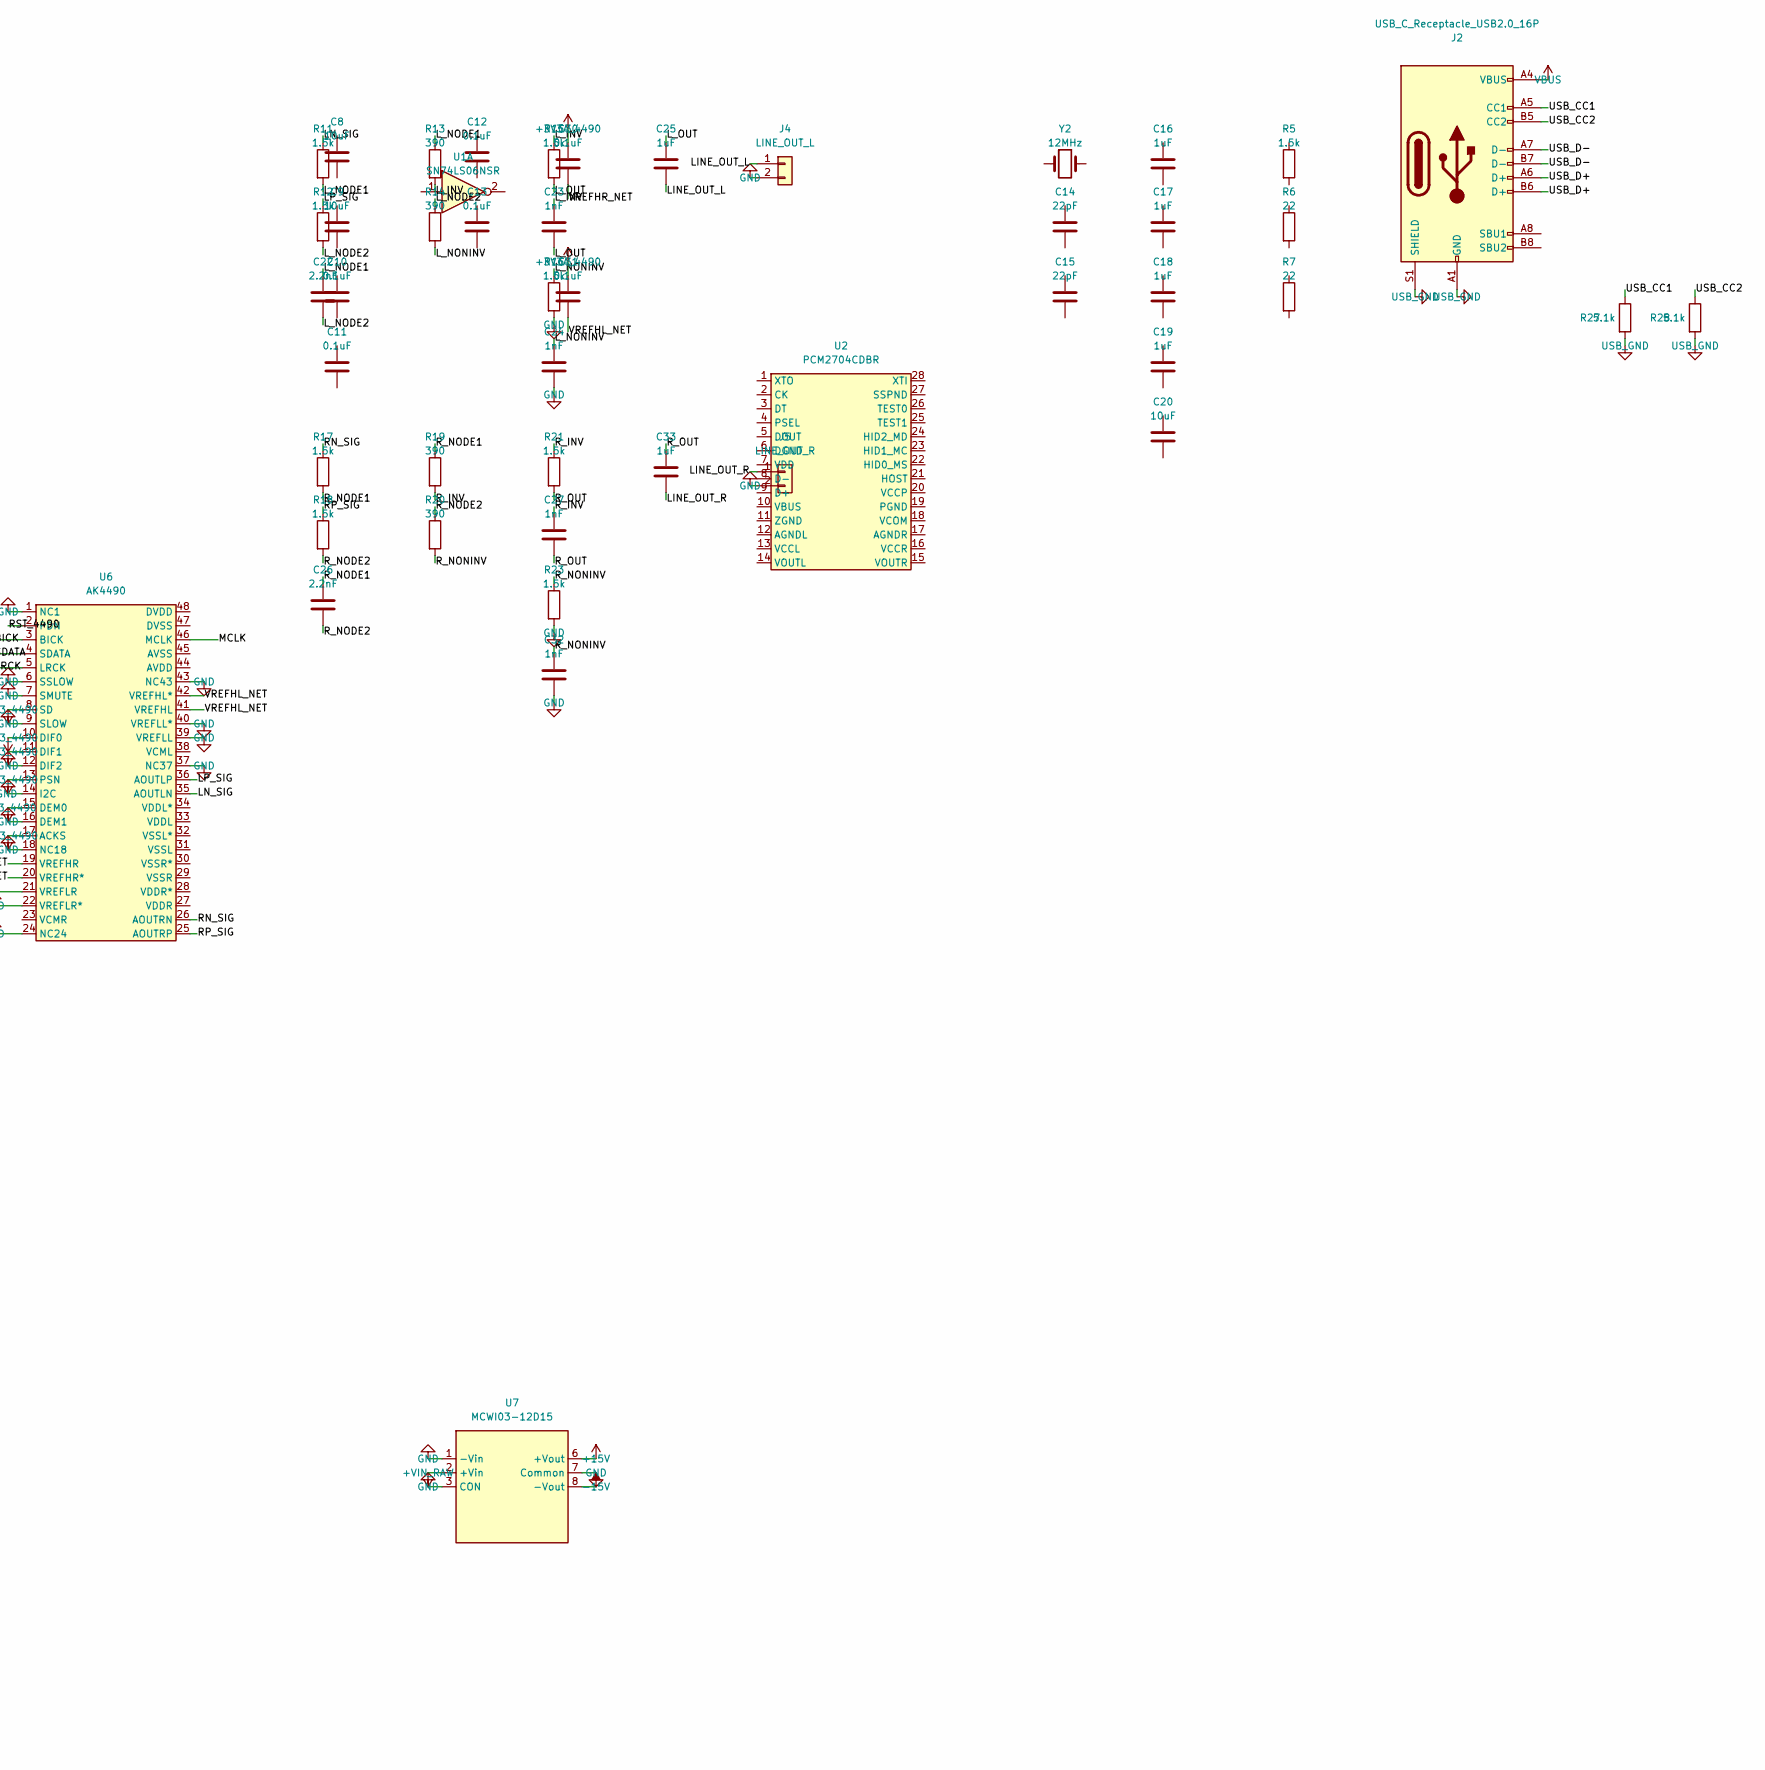
[picture p33: schematic before.kicad_sch, part in row 1, column 2]

Parts:
C1, C2: 18pF; C_0603_1608Metric
C3: 0.47uF; C_0603_1608Metric
C4, C5, C6, C7, C10, C11, C12, C13, C21, C28, C29, C30, C31: 0.1uF; C_0603_1608Metric
C8, C9, C20: 10uF; C_0805_2012Metric
C14, C15: 22pF; C_0603_1608Metric
C16, C17, C18, C19, C25, C33: 1uF; C_0603_1608Metric
C22, C26: 2.2nF; C_0603_1608Metric
C23, C24, C27, C32: 1nF; C_0603_1608Metric
IC1, IC2, IC3: LP5907MFX-3.3/NOPB; SOT-23-5
IC4, IC8: TPS7A2050PDBVR; SOT-23-5
IC5: MUSES8920; DIP-8_W7.62mm
IC9: AMS1117; SOT-223-3_TabPin2
J1: JST_XA_B02B-XASK-1; JST_XA_B02B-XASK-1_1x02_P2.50mm_Vertical
J2: USB_C_Receptacle_USB2.0_16P; USB_C_Receptacle_GCT_USB4085
J3: TORX147FT
J4: LINE_OUT_L
J5: LINE_OUT_R
JP1: IPS0_SEL; PinHeader_1x03_P2.54mm_Vertical
R1: 10k; R_0603_1608Metric
R2: 470; R_0603_1608Metric
R3, R8: 240; R_0603_1608Metric
R4: 820; R_0603_1608Metric
R5, R11, R12, R15, R16, R17, R18, R21, R23: 1.5k; R_0603_1608Metric
R6, R7: 22; R_0603_1608Metric
R9: 120; R_0603_1608Metric
R10: 75; R_0603_1608Metric
R13, R14, R19, R20: 390; R_0603_1608Metric
R25, R26: 100k; R_0603_1608Metric
R27, R28: 5.1k; R_0603_1608Metric
T1: DA103C; DA103C_MUR
U1: SN74LS06NSR; SOIC-14_3.9x8.7mm_P1.27mm
U2: PCM2704CDBR; SSOP-28_5.3x10.2mm_P0.65mm
U3, U4: TCM809TENB713; SOT-23
U5: AK4118; LQFP-48_7x7mm_P0.5mm
U6: AK4490; LQFP-48_7x7mm_P0.5mm
U7: MCWI03-12D15
Y1: 11.2896MHz; Crystal_SMD_5032-2Pin_5.0x3.2mm
Y2: 12MHz; Crystal_SMD_3225-4Pin_3.2x2.5mm

Connections:
+3V3A_4490: C30.1, C31.1
+3V3_118: C4.1, C28.1, J3.3 (Vcc), U3.3 (V_{DD}), U5.3 (DIF0), U5.7 (DIF2), U5.9 (PSN)
+3V3_4490: C29.1, U4.3 (V_{DD}), U6.8 (SD), U6.10 (DIF0), U6.11 (DIF1), U6.13 (PSN), U6.15 (DEM0), U6.17 (ACKS)
+15V: IC5.8 (V+), U7.6 (+Vout)
+VIN_RAW: J1.1, U7.2 (+Vin)
-15V: IC5.4 (V-), U7.8 (-Vout)
BICK: U5.26 (BICK), U6.3 (BICK)
GND: C4.2, C24.2, C28.2, C29.2, C32.2, J1.2, J3.2 (GND), J4.2, J5.2, R16.2, R23.2, R25.2, R26.2, U3.1 (GND), U4.1 (GND), U5.2 (NC2), U5.4 (TEST2), U5.5 (DIF1), U5.8 (IPS1), U5.10 (XTL0), U5.11 (XTL1), U5.12 (VIN), U5.14 (GP1), U5.32 (CM0), U5.33 (CM1), U5.34 (OCKS1), U5.35 (OCKS0), U5.43 (NC43), U5.45 (TEST1), U6.1 (NC1), U6.6 (SSLOW), U6.7 (SMUTE), U6.9 (SLOW), U6.12 (DIF2), U6.14 (I2C), U6.16 (DEM1), U6.18 (NC18), U6.21 (VREFLR), U6.22 (VREFLR*), U6.24 (NC24), U6.37 (NC37), U6.39 (VREFLL), U6.40 (VREFLL*), U6.43 (NC43), U7.1 (-Vin), U7.3 (CON), U7.7 (Common)
LINE_OUT_L: C25.2, J4.1
LINE_OUT_R: C33.2, J5.1
LN_SIG: R11.1, U6.35 (AOUTLN)
LP_SIG: R12.1, U6.36 (AOUTLP)
LRCK: U5.24 (LRCK), U6.5 (LRCK)
L_INV: C23.1, IC5.2 (-), R13.2, R15.1
L_NODE1: C22.1, R11.2, R13.1
L_NODE2: C22.2, R12.2, R14.1
L_NONINV: C24.1, IC5.3 (+), R14.2, R16.1
L_OUT: C23.2, C25.1, IC5.1, R15.2
MCLK: U5.23 (MCKO1), U6.46 (MCLK)
RN_SIG: R17.1, U6.26 (AOUTRN)
RP_SIG: R18.1, U6.25 (AOUTRP)
RST_118: R25.1, U3.2 (~RESET), U5.31 (PDN)
RST_4490: R26.1, U4.2 (~RESET), U6.2 (PDN)
RX0: R2.2, U5.42 (RX0)
R_INV: C27.1, IC5.6 (-), R19.2, R21.1
R_NODE1: C26.1, R17.2, R19.1
R_NODE2: C26.2, R18.2, R20.1
R_NONINV: C32.1, IC5.5 (+), R20.2, R23.1
R_OUT: C27.2, C33.1, IC5.7, R21.2
SDATA: U5.25 (SDTO), U6.4 (SDATA)
SPDIF_OPT: J3.1 (Output), R2.1
USB_CC1: J2.A5 (CC1), R27.1
USB_CC2: J2.B5 (CC2), R28.1
USB_D+: J2.A6 (D+), J2.B6 (D+)
USB_D-: J2.A7 (D-), J2.B7 (D-)
USB_GND: J2.A1 (GND), J2.A12 (GND), J2.B1 (GND), J2.B12 (GND), J2.S1 (SHIELD), R27.2, R28.2
VBUS: J2.A4 (VBUS), J2.A9 (VBUS), J2.B4 (VBUS), J2.B9 (VBUS)
VREFHL_NET: C31.2, U6.41 (VREFHL), U6.42 (VREFHL*)
VREFHR_NET: C30.2, U6.19 (VREFHR), U6.20 (VREFHR*)
